agumurray/G8-TP1/firmware_v3/documentation/firmware/eclipse/Eclipse-Win14.png

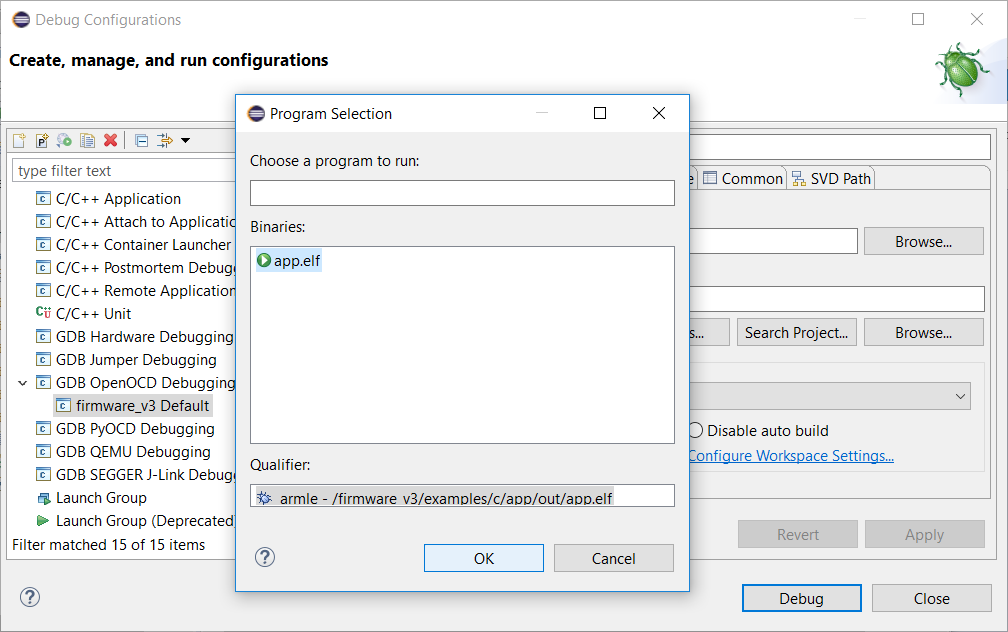
firmware_v3/documentation/firmware/eclipse/Eclipse-Win14.png
