agumurray/G8-TP1/firmware_v3/documentation/firmware/eclipse/targets-02.png

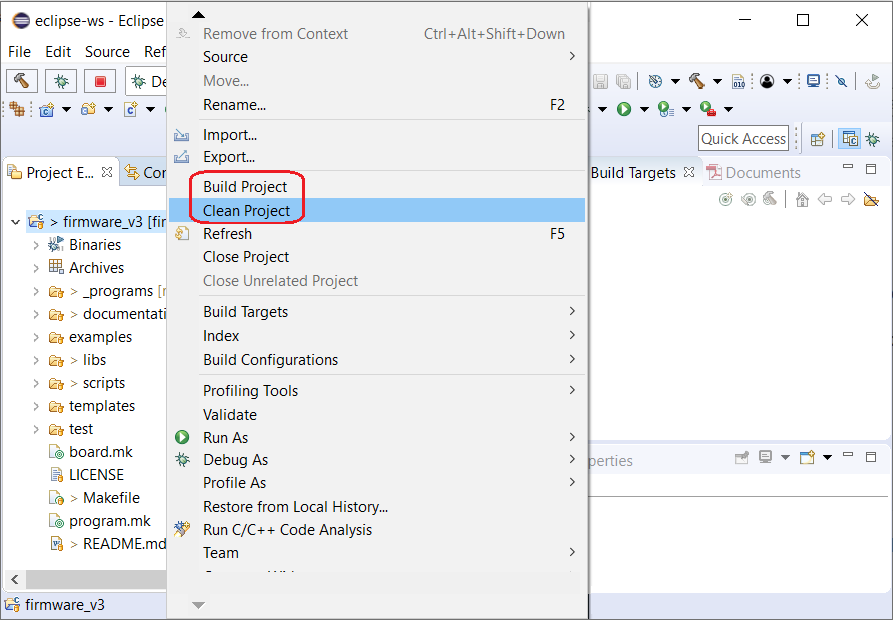
firmware_v3/documentation/firmware/eclipse/targets-02.png
