agumurray/G8-TP1/firmware_v3/documentation/firmware/embedded_ide/open02.png

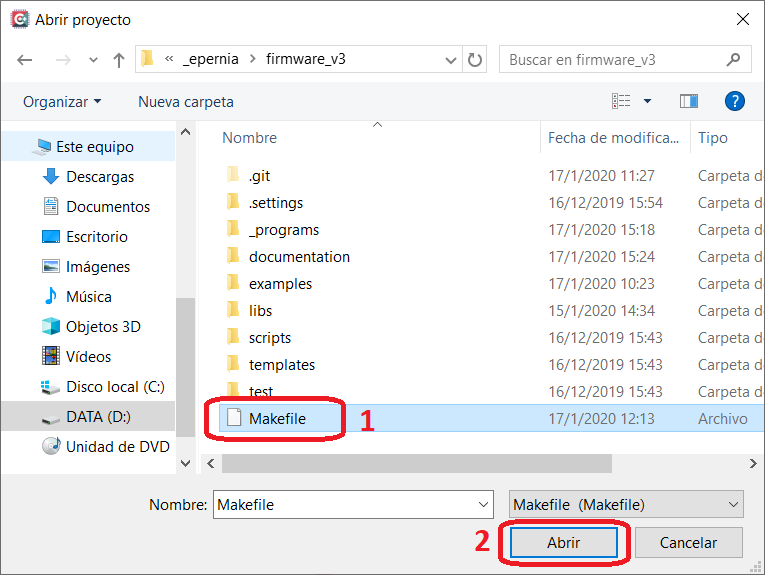
firmware_v3/documentation/firmware/embedded_ide/open02.png
