agumurray/G8-TP1/firmware_v3/test/test_hcsr04/sapi/adc_dac/adc_analog_stick_connection.png

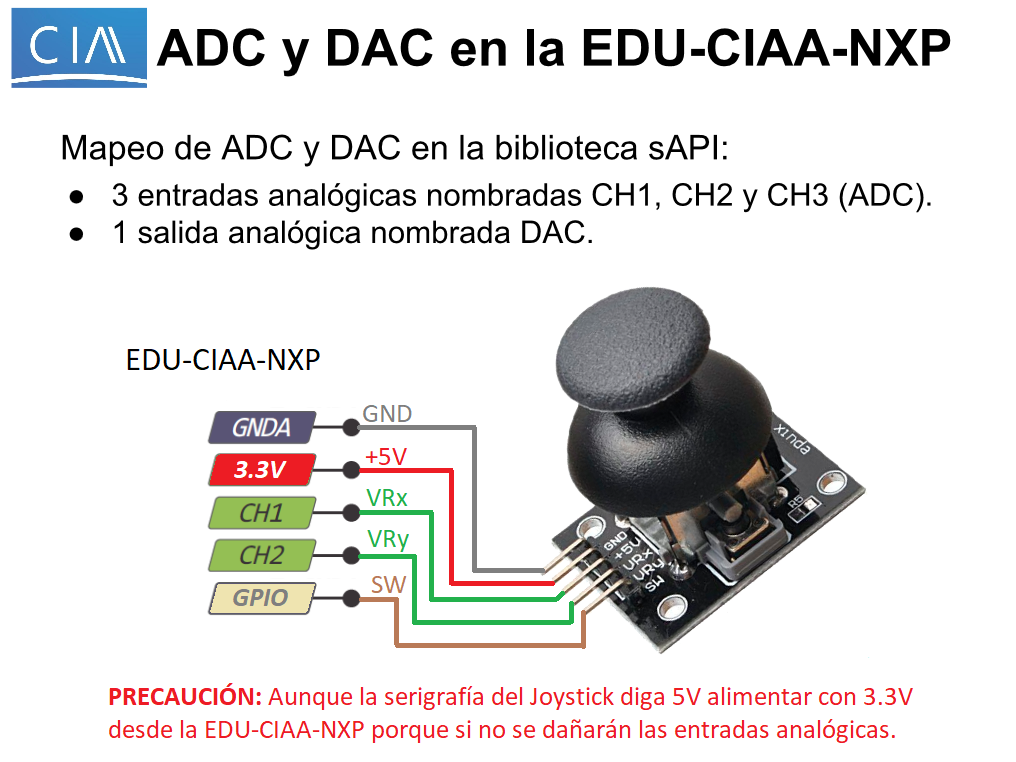
firmware_v3/test/test_hcsr04/sapi/adc_dac/adc_analog_stick_connection.png
