agumurray/G8-TP1/firmware_v3/test/test_hcsr04/sapi/bluetooth/hc05_uart_bridge/bluetooth_hc05_connection.png

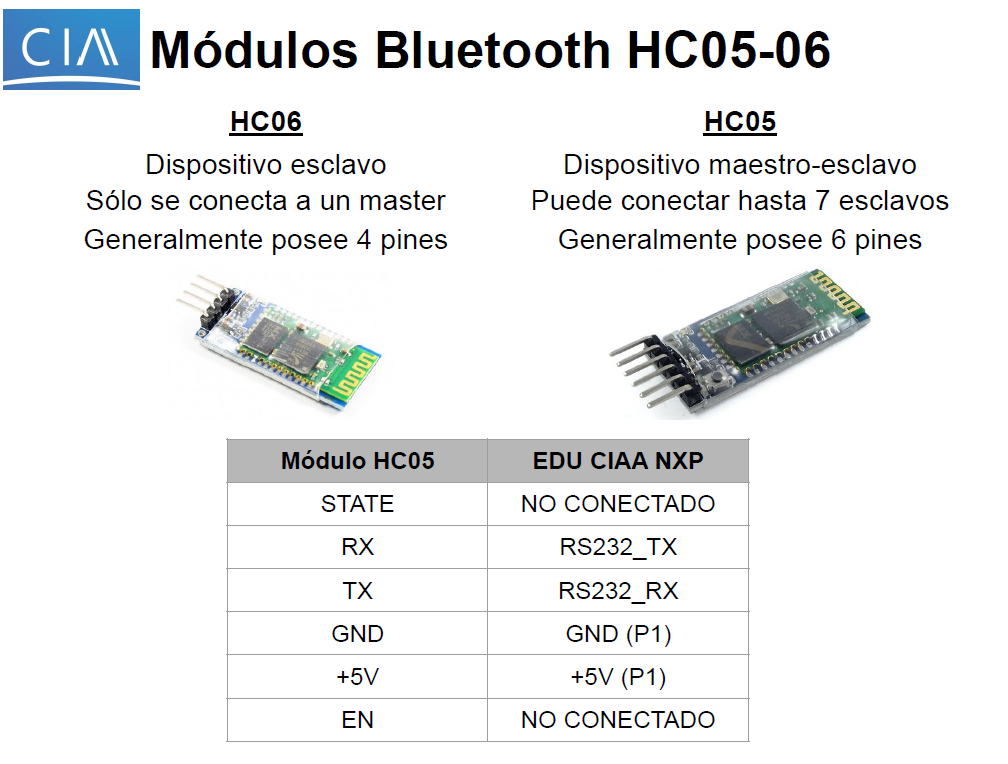
firmware_v3/test/test_hcsr04/sapi/bluetooth/hc05_uart_bridge/bluetooth_hc05_connection.png
