agumurray/G8-TP1/firmware_v3/test/test_hcsr04/sapi/bluetooth/hm10_uart_bridge/bluetooth_ble_hm10_connection.png

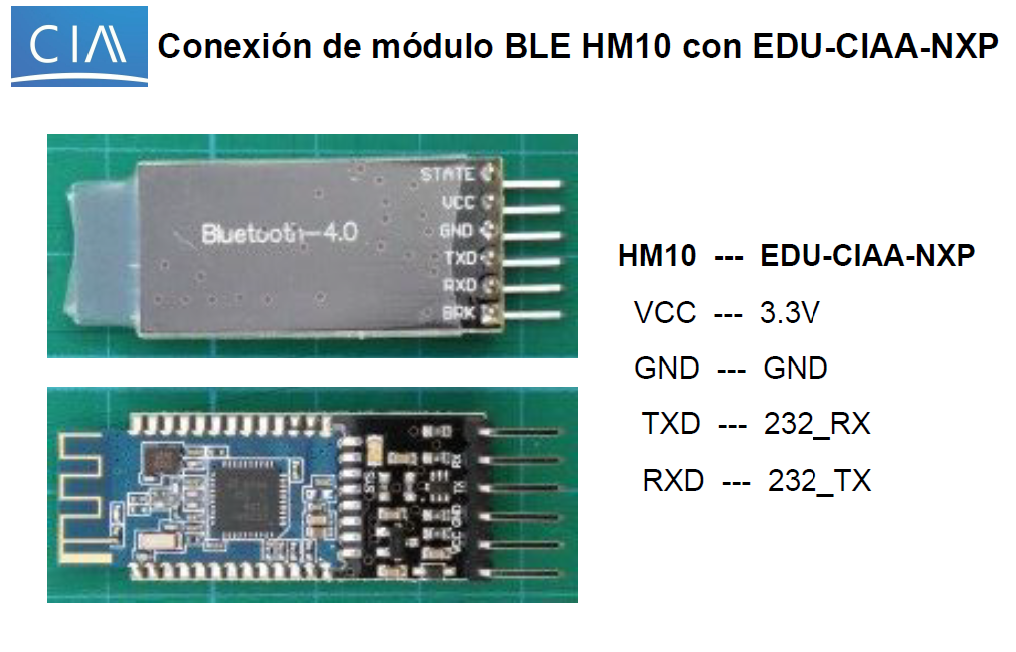
firmware_v3/test/test_hcsr04/sapi/bluetooth/hm10_uart_bridge/bluetooth_ble_hm10_connection.png
