agumurray/G8-TP1/firmware_v3/test/test_hcsr04/sapi/dht11_temp_humidity/DHT11 and EDU-CIAA-NXP.png

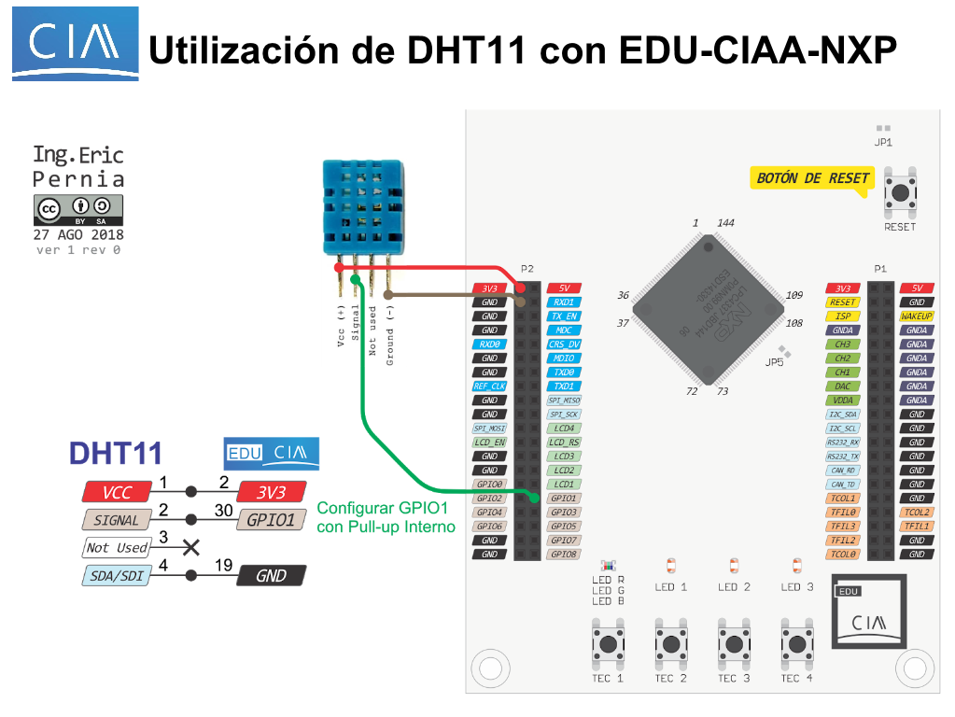
firmware_v3/test/test_hcsr04/sapi/dht11_temp_humidity/DHT11 and EDU-CIAA-NXP.png
