agumurray/G8-TP1/firmware_v3/test/test_hcsr04/sapi/fatfs_sdcard_usbmsd/SD SPI.png

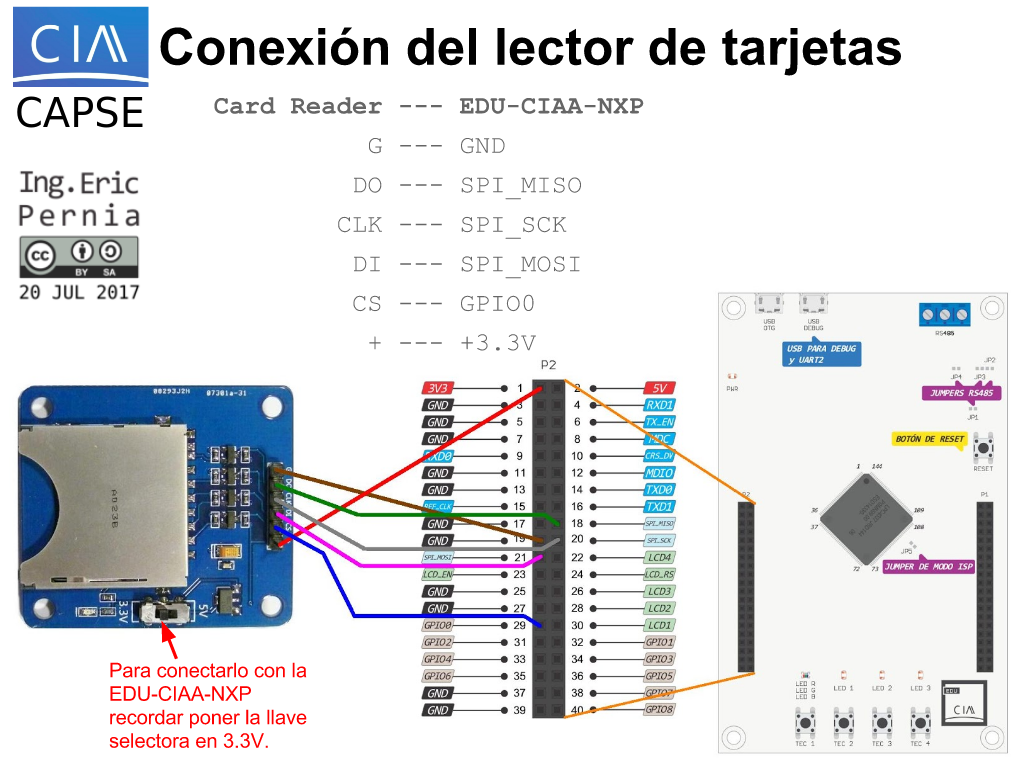
firmware_v3/test/test_hcsr04/sapi/fatfs_sdcard_usbmsd/SD SPI.png
