agumurray/G8-TP1/firmware_v3/test/test_hcsr04/sapi/gpio/axis_interface/AXI Stream.png

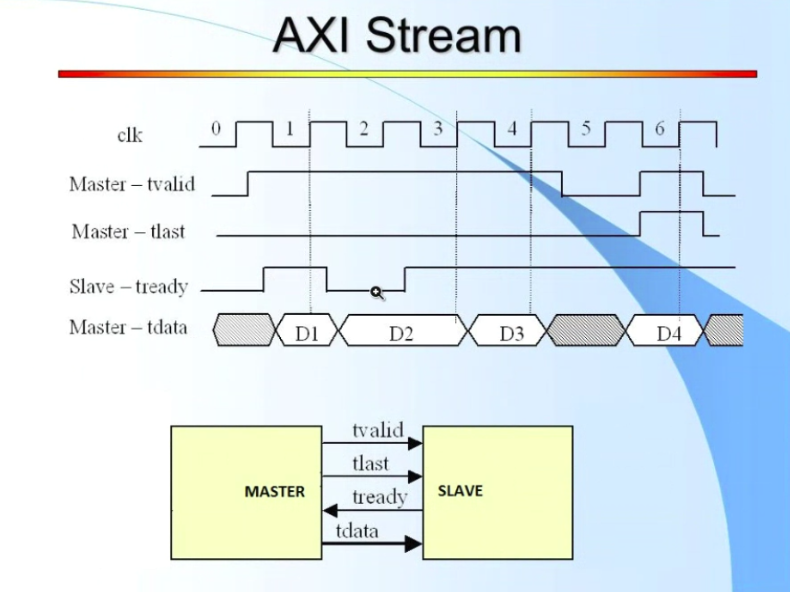
firmware_v3/test/test_hcsr04/sapi/gpio/axis_interface/AXI Stream.png
