agumurray/G8-TP1/firmware_v3/test/test_hcsr04/sapi/gpio/axis_interface/axis_pins_edu_ciaa.png

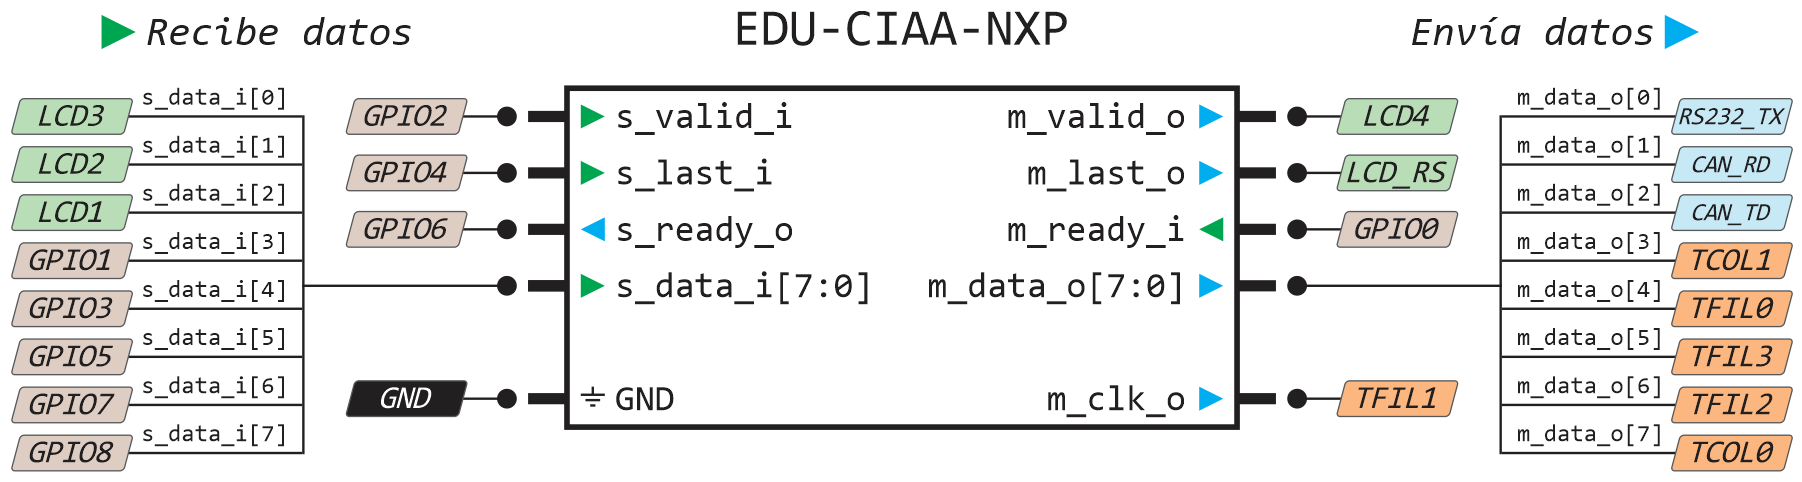
firmware_v3/test/test_hcsr04/sapi/gpio/axis_interface/axis_pins_edu_ciaa.png
