agumurray/G8-TP1/firmware_v3/test/test_hcsr04/sapi/hcsr04_ultrasonic_sensor/Conexión EDU-CIAA - HC-SR04.png

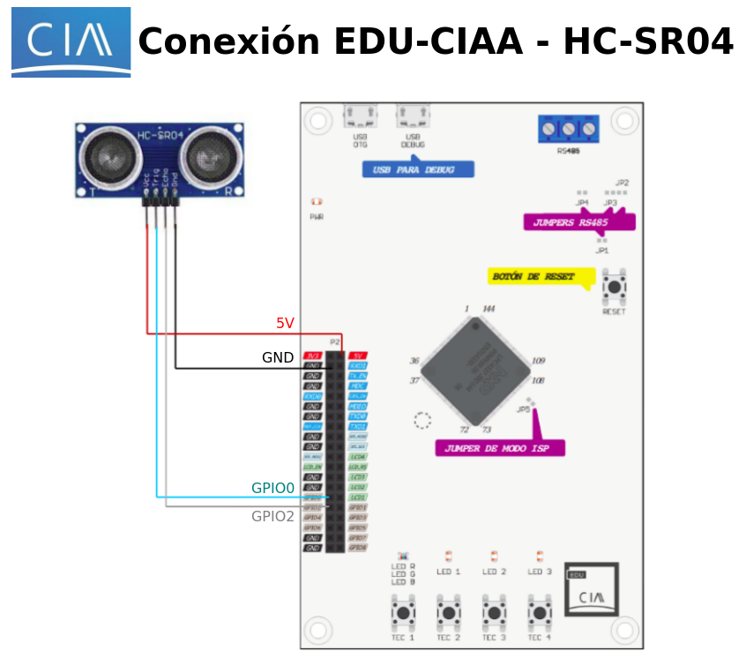
firmware_v3/test/test_hcsr04/sapi/hcsr04_ultrasonic_sensor/Conexión EDU-CIAA - HC-SR04.png
