agumurray/G8-TP1/firmware_v3/test/test_hcsr04/sapi/i2c/IMUs/mpu9250/MPU9250 and EDU-CIAA-NXP.png

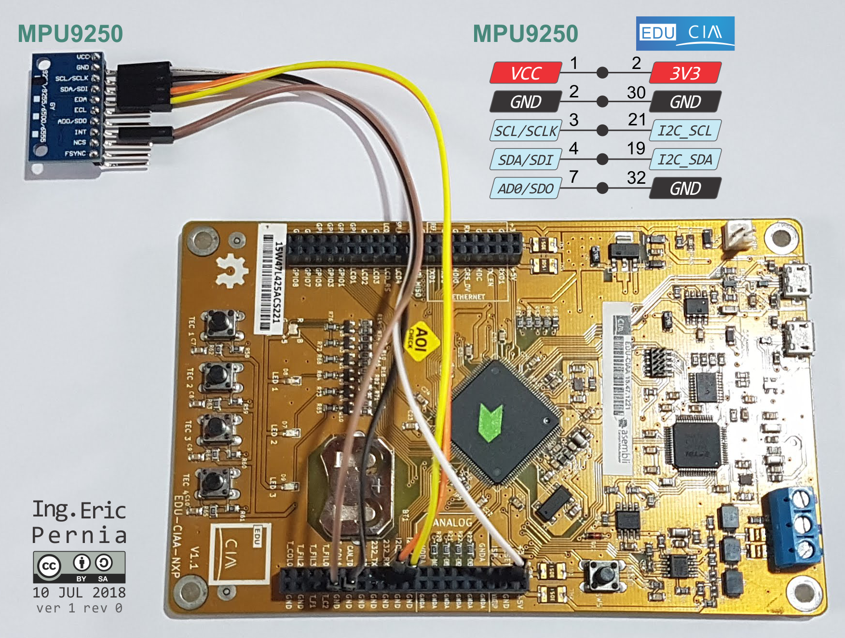
firmware_v3/test/test_hcsr04/sapi/i2c/IMUs/mpu9250/MPU9250 and EDU-CIAA-NXP.png
