agumurray/G8-TP1/firmware_v3/test/test_hcsr04/sapi/i2c/IMUs/mpu9250/Serial Terminal - MPU9250 working.PNG

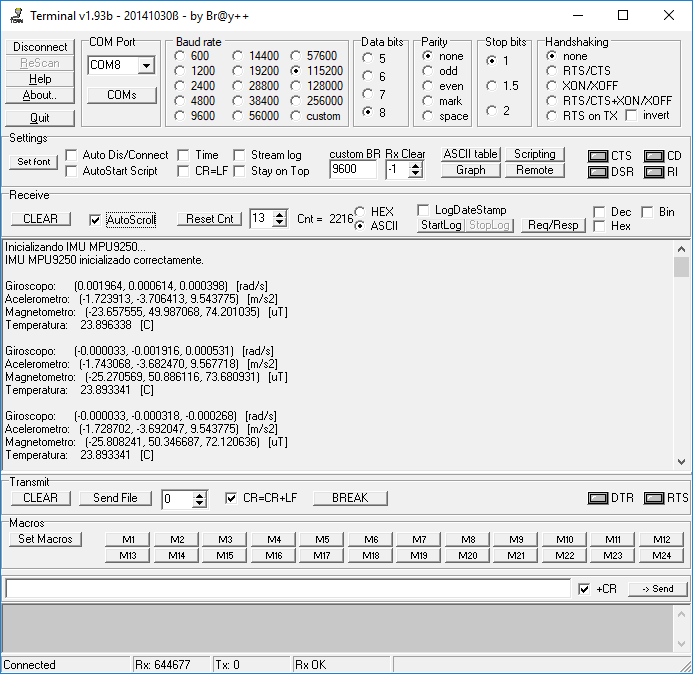
firmware_v3/test/test_hcsr04/sapi/i2c/IMUs/mpu9250/Serial Terminal - MPU9250 working.PNG
