agumurray/G8-TP1/firmware_v3/test/test_hcsr04/sapi/i2c/magnetometers/hmc5883l/HMC5883L_EDU-CIAA.png

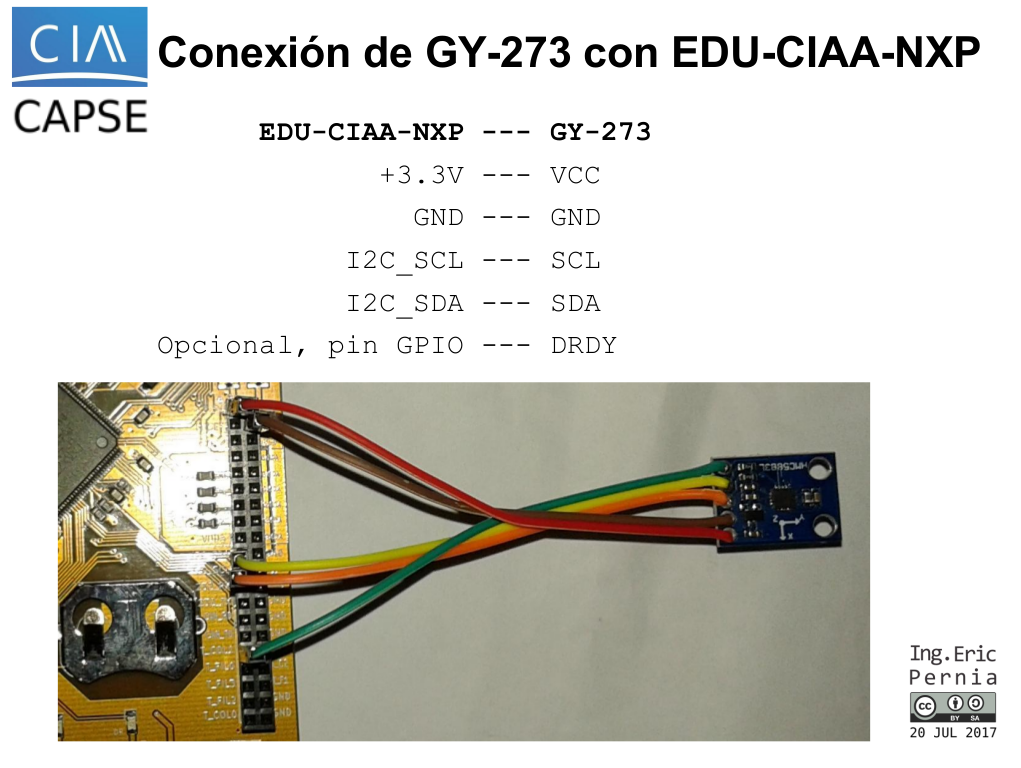
firmware_v3/test/test_hcsr04/sapi/i2c/magnetometers/hmc5883l/HMC5883L_EDU-CIAA.png
