agumurray/G8-TP1/firmware_v3/test/test_hcsr04/sapi/keypad_7segment/7 segment display - EDU-CIAA-NXP.png

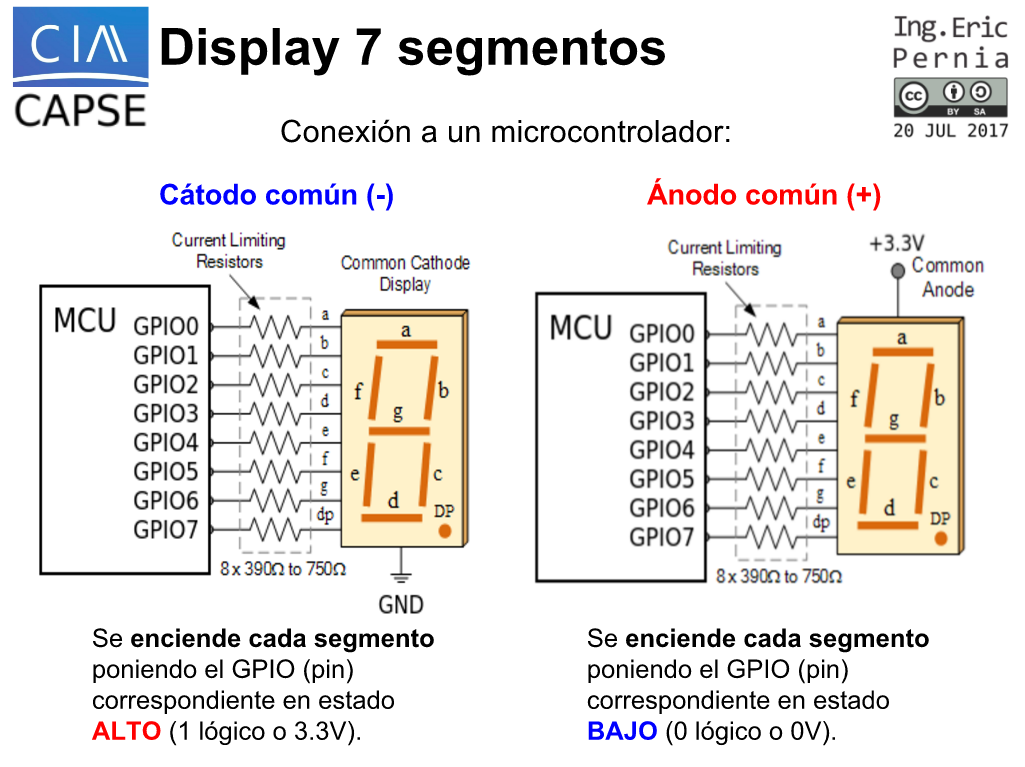
firmware_v3/test/test_hcsr04/sapi/keypad_7segment/7 segment display - EDU-CIAA-NXP.png
