agumurray/G8-TP1/firmware_v3/test/test_hcsr04/sapi/lcd/lcd info/LCD HD44780 connection.png

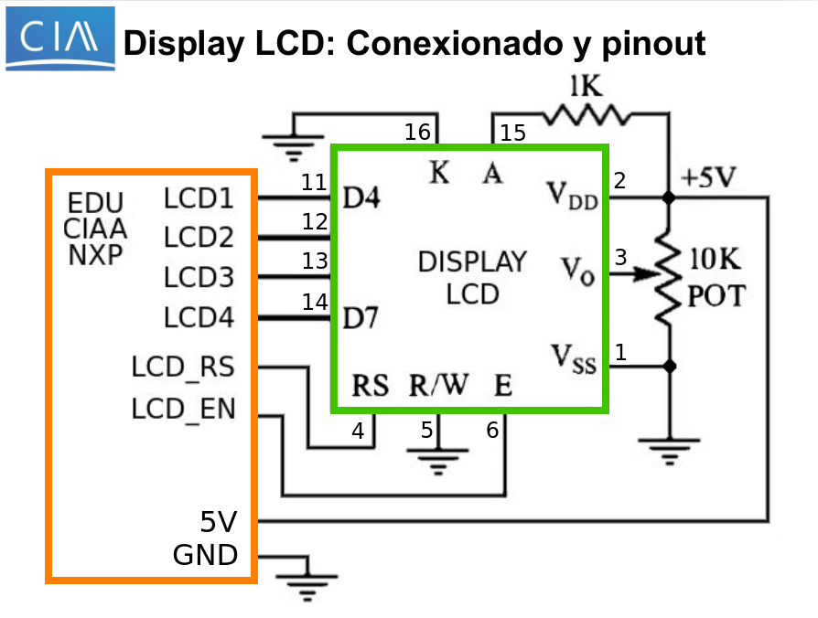
firmware_v3/test/test_hcsr04/sapi/lcd/lcd info/LCD HD44780 connection.png
