agumurray/G8-TP1/firmware_v3/test/test_hcsr04/sapi/lcd/lcd_i2c/I2C expander PCF8574/Encapsulado en placa.png

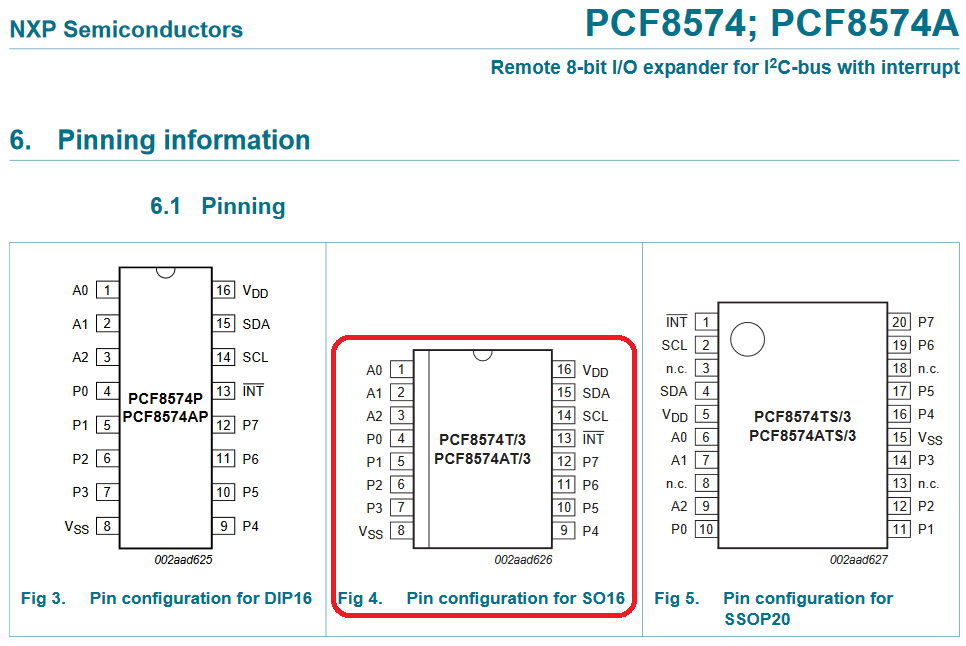
firmware_v3/test/test_hcsr04/sapi/lcd/lcd_i2c/I2C expander PCF8574/Encapsulado en placa.png
