agumurray/G8-TP1/firmware_v3/test/test_hcsr04/sapi/servo/servo_connection.png

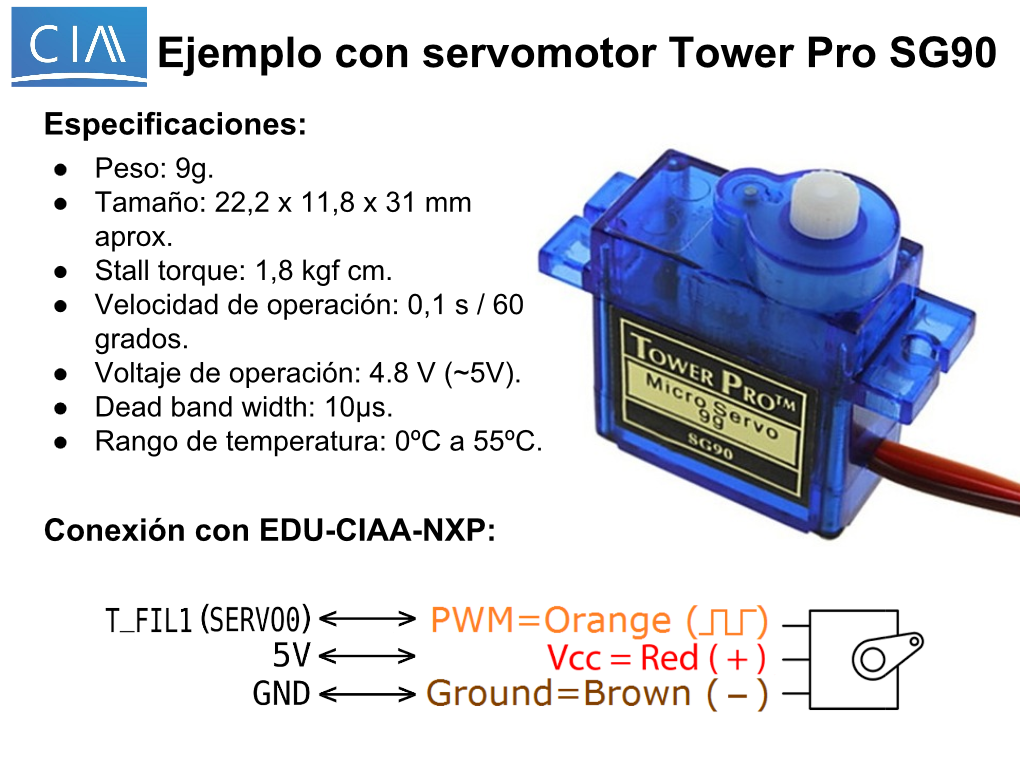
firmware_v3/test/test_hcsr04/sapi/servo/servo_connection.png
