agumurray/G8-TP1/firmware_v3/test/test_hcsr04/sapi/servo/servo_pins.png

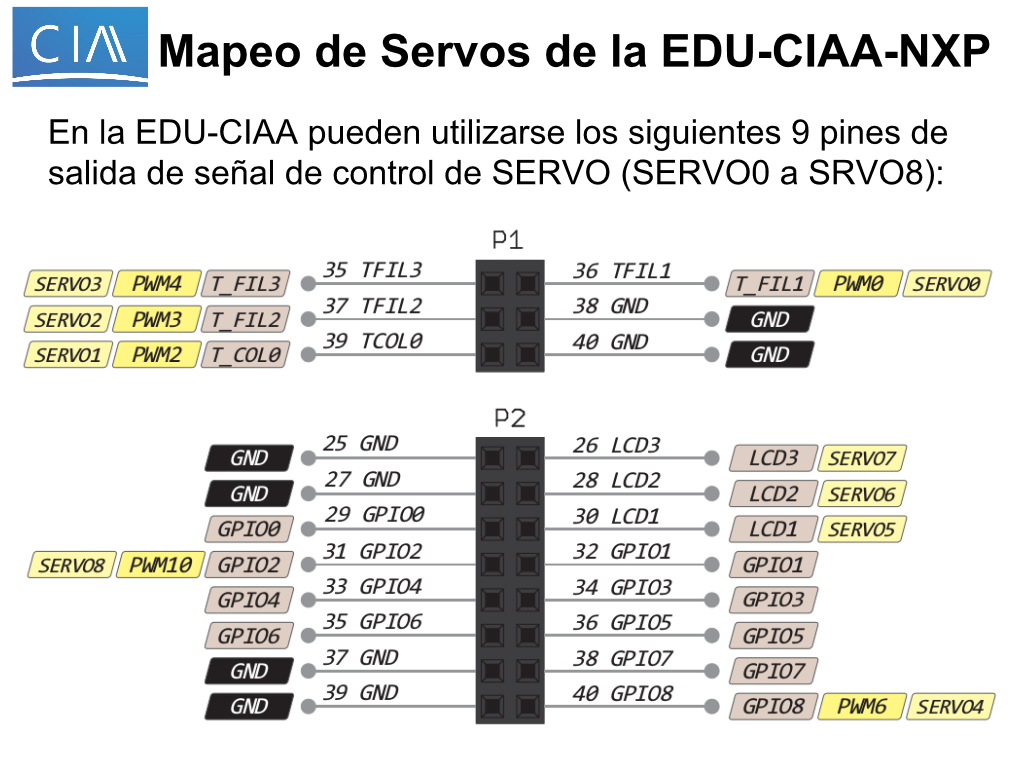
firmware_v3/test/test_hcsr04/sapi/servo/servo_pins.png
