agumurray/G8-TP1/firmware_v3/test/test_hcsr04/sapi/wifi/esp8266/Conexion ESP8266 y EDU-CIAA.png

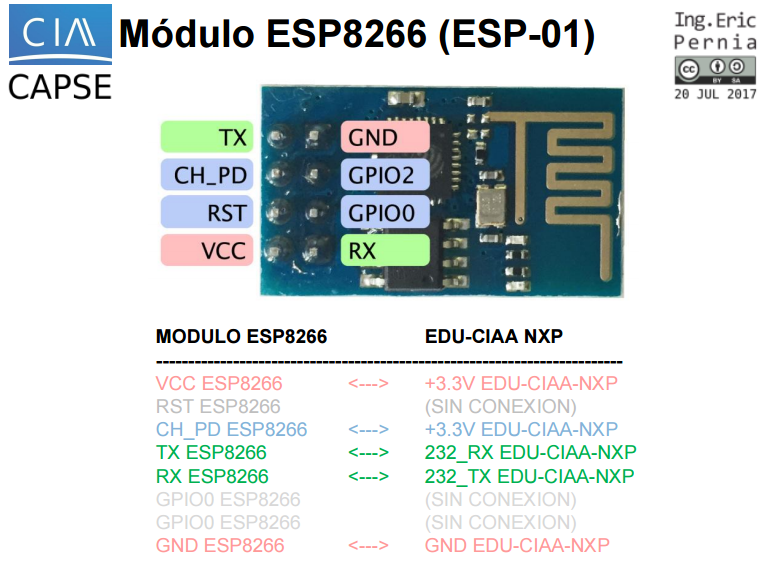
firmware_v3/test/test_hcsr04/sapi/wifi/esp8266/Conexion ESP8266 y EDU-CIAA.png
