agumurray/G8-TP1/firmware_v3/test/test_hcsr04/sapi/wifi/esp8266/iot_thingspeak/Datos en Thingspeak.png

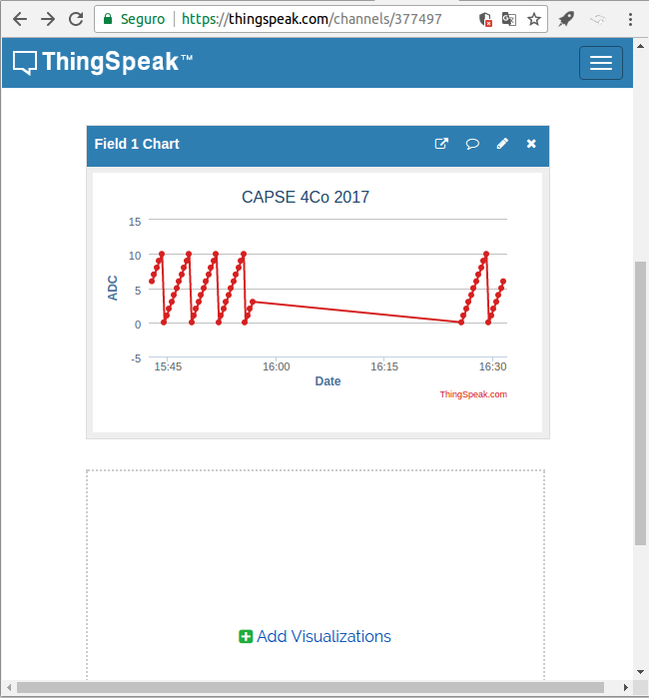
firmware_v3/test/test_hcsr04/sapi/wifi/esp8266/iot_thingspeak/Datos en Thingspeak.png
