agumurray/G8-TP1/firmware_v3/test/test_hcsr04/sapi/adc_dac/EDU-CIAA-NXP Tiras de pines y Potenciómetro.pdf

## EDU-CIAA-NXP Preparación de placa con Tiras de pines hembra y Potenciómetro

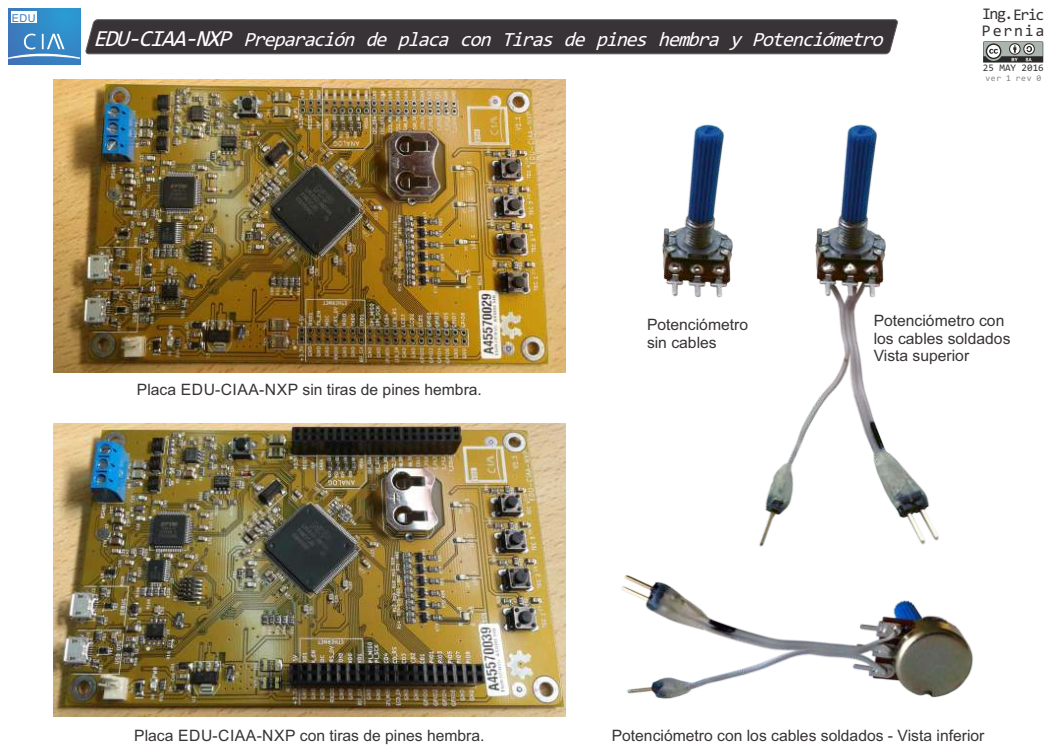
[picture p180: page 1]
EDU; Potenciómetro sin cables; 25 MAY 2016 ver 1 rev 0; Pernia; Ing.Eric

Potenciómetro con
los cables soldados
Vista superior

Placa EDU-CIAA-NXP sin tiras de pines hembra.

Placa EDU-CIAA-NXP con tiras de pines hembra.

Potenciómetro con los cables soldados - Vista inferior

## EDU-CIAA-NXP Conexión de potenciómetro

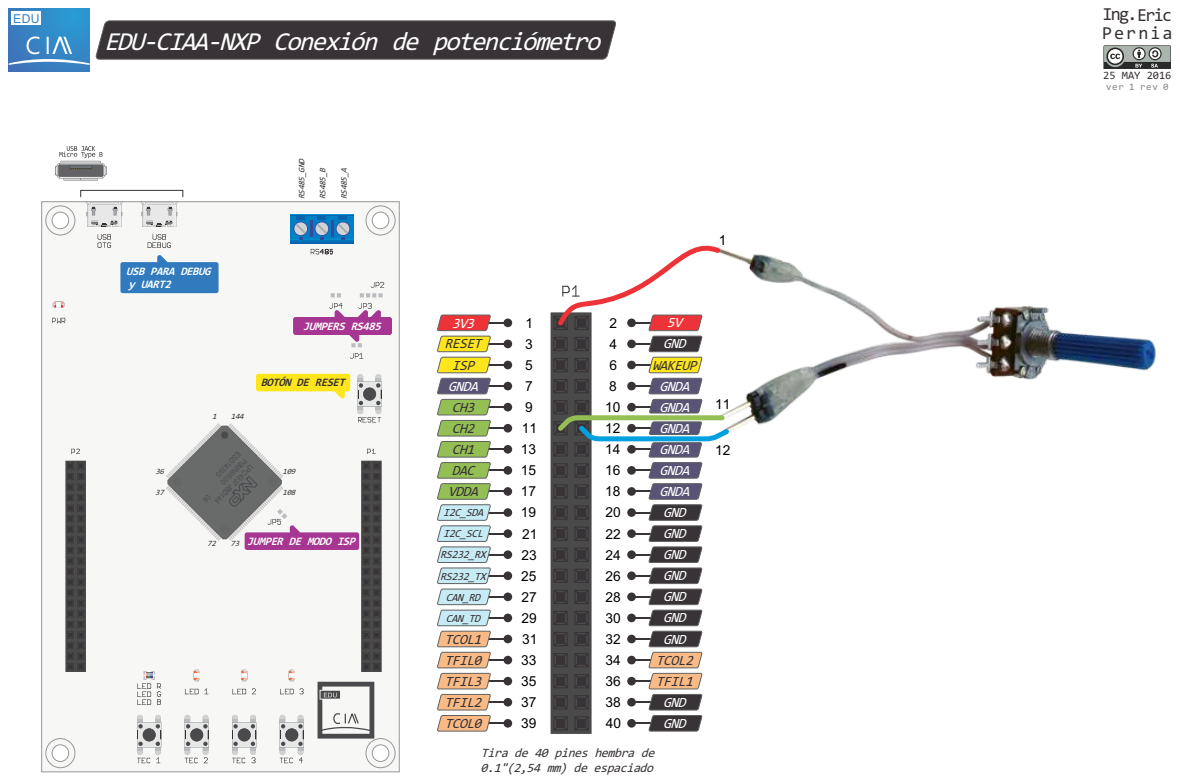
[picture p181: page 2]
EDU; 25 MAY 2016 ver 1 rev 0; Pernia; Ing.Eric; LPC4337 JBD144; ESD14330-; JUMPER DE MODO ISP; JUMPERS RS485; RS485_GND; GND; GNDA; WAKEUP; TCOL2; TFIL1; TCOL1; TFIL0; TFIL3; TFIL2; TCOL0; ISP; RESET; DAC; VDDA; I2C_SDA; I2C_SCL; CAN_RD; CAN_TD

USB PARA DEBUG
y UART2

BOTÓN DE RESET

Tira de 40 pines hembra de
0.1"(2,54 mm) de espaciado
