agumurray/G8-TP1/firmware_v3/documentation/CIAA_Boards/NXP_LPC4337/CIAA-NXP/CIAA-NXP Esquematico.pdf

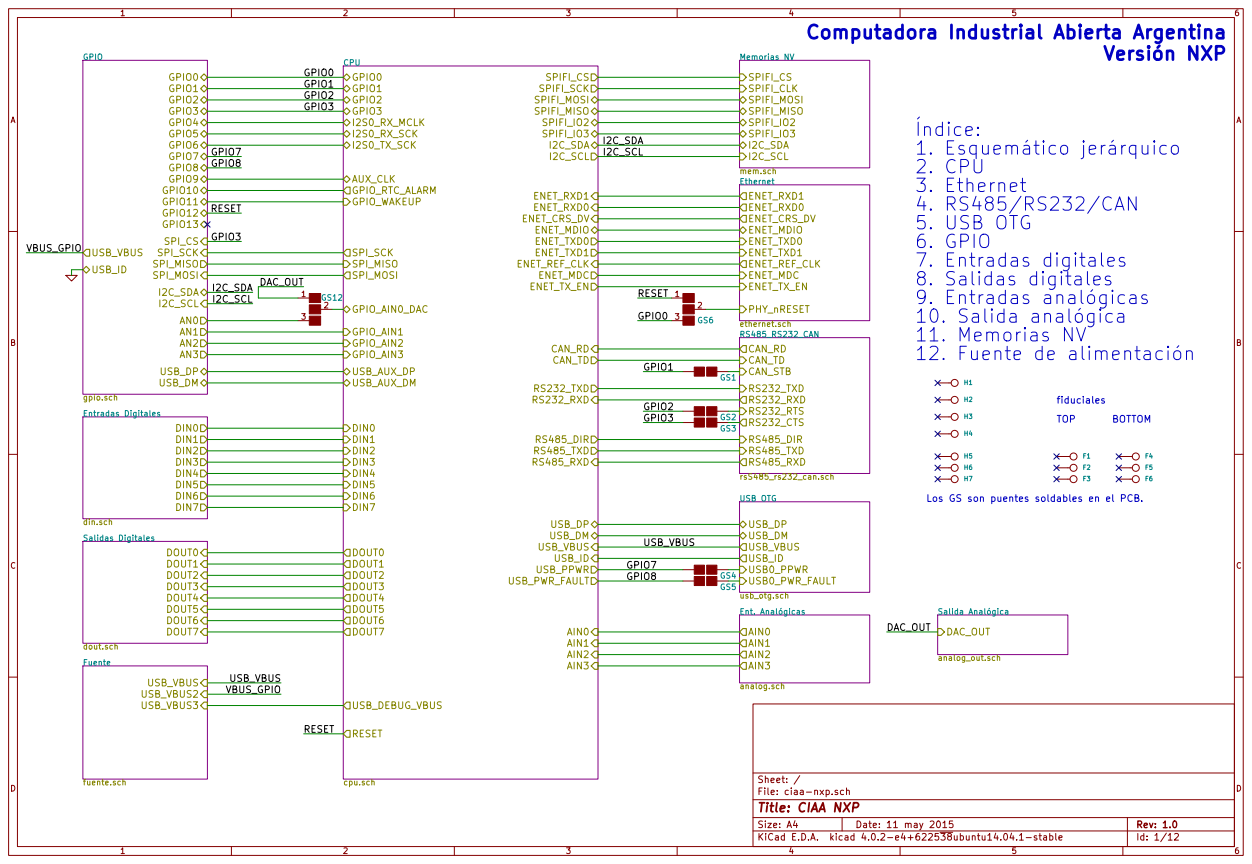
[picture p182: page 1]

Computadora Industrial Abierta Argentina

GPIO1
GPIO2
GPIO3

File: ciaa-nxp.sch Sheet: /
Id: 1/12 Title: CIAA NXP

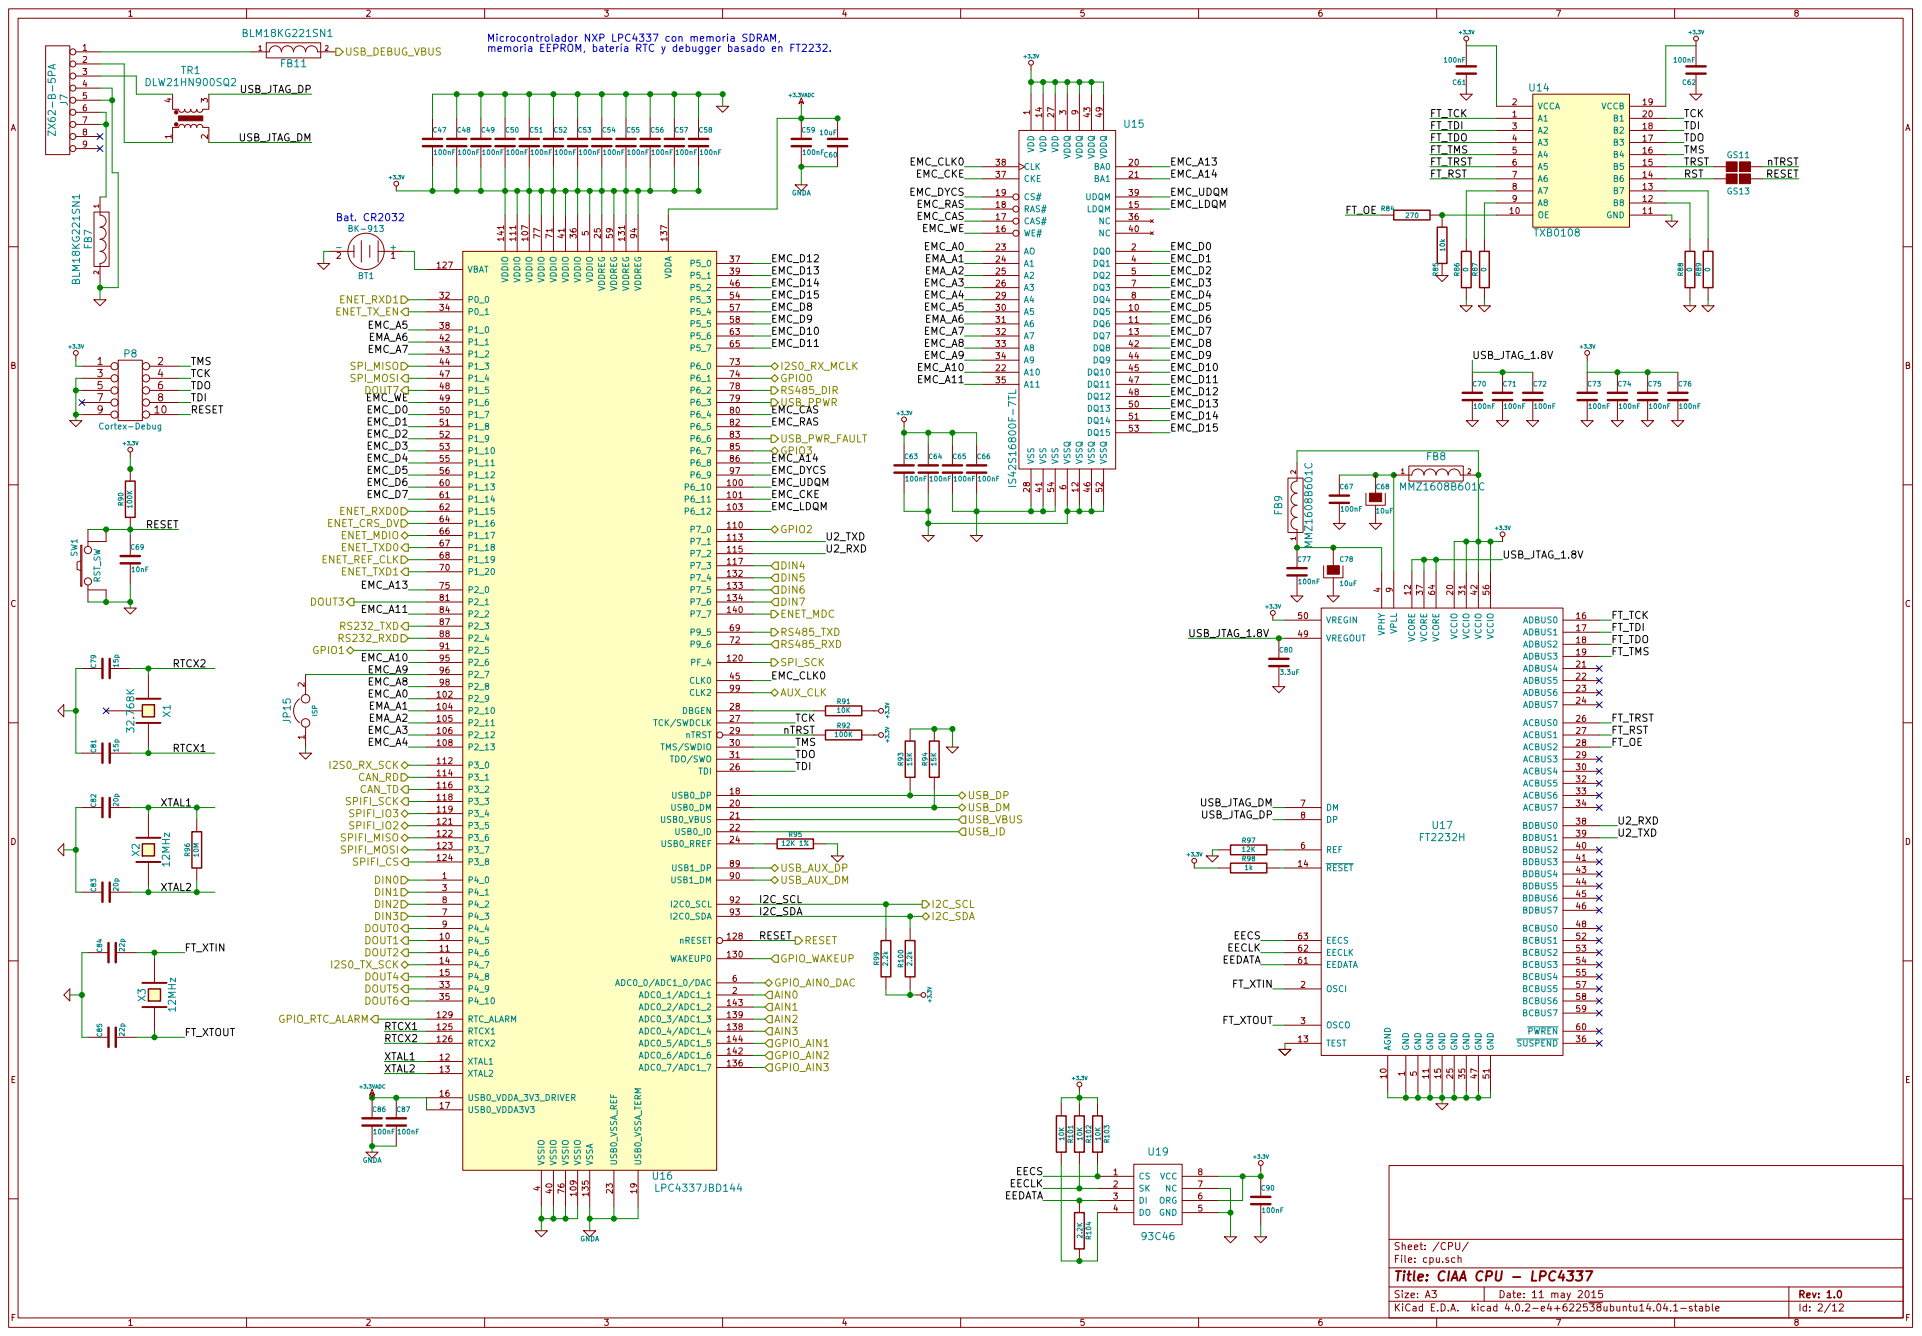
[picture p183: page 2]

memoria EEPROM, batería RTC y debugger basado en FT2232.

9 DQ5 10 BA0 20 A5 30 NC 40 DQ13 50 DQ6 11 BA1 21 A6 31 VSS 41 DQ14 51 VSSQ 12 A10 22 A7 32 DQ8 42 VSSQ 52 DQ7 13 AO 23 A8 33 VDDQ 43 DQ15 53 VDD 14 A1 24 A9 34 DQ9 44 VSS 54

FT_TMS | 20 GND 16 B3
FT_TDO | 17 B2

FT_TRST | | 15 B4
FT_RST | 14 B5

5 ADC0_0/ADC1_0/DAC 6 P4_3 7 P4_2 8 P4_4 9 P4_5 10 USB0_DM 20 TMS/SWDIO 30 VSSIO 40 P1_7 50 P1_13 60 P1_20 70 P6_4 80 USB1_DM 90 P4_6 11 USB0_VBUS 21 TDO/SWO 31 VDDIO 41 P1_8 51 P1_14 61 VDDIO 71 P2_1 81 P2_5 91 XTAL1 12 USB0_ID 22

9 AGND 10 VCCIO 20 ACBUS4 30 BDBUS2 40 VREGIN 50 PWREN 60 GND 11 ADBUS4 21 VCCIO 31 BDBUS3 41 GND 51 EEDATA 61 VCORE 12 ADBUS5 22 ACBUS5 32 VCCIO 42 BCBUS1 52 EECLK 62 TEST 13 ADBUS6 23 ACBUS6 33 BDBUS4 43 BCBUS2 53 EECS 63 RESET 14 ADBUS7 24 ACBUS7 34 BDBUS5 44 BCBUS3 54 VCORE 64 GND 15 GND 25 GND 35 BDBUS6 45 BCBUS4 55 ADBUS0 16 ACBUS0 26 SUSPEND 36 BDBUS7 46 VCCIO 56 ADBUS1 17 ACBUS1 27 VCORE 37 GND 47 BCBUS5 57 ADBUS2 18 ACBUS2 28 BDBUS0 38 BCBUS0 48 BCBUS6 58 ADBUS3 19 ACBUS3 29 BDBUS1 39 VREGOUT 49 BCBUS7 59 U17 FT2232H

5 REF 6 DM 7 DP 8 VPLL

File: cpu.sch Sheet: /CPU/
Id: 2/12 Title: CIAA CPU - LPC4337

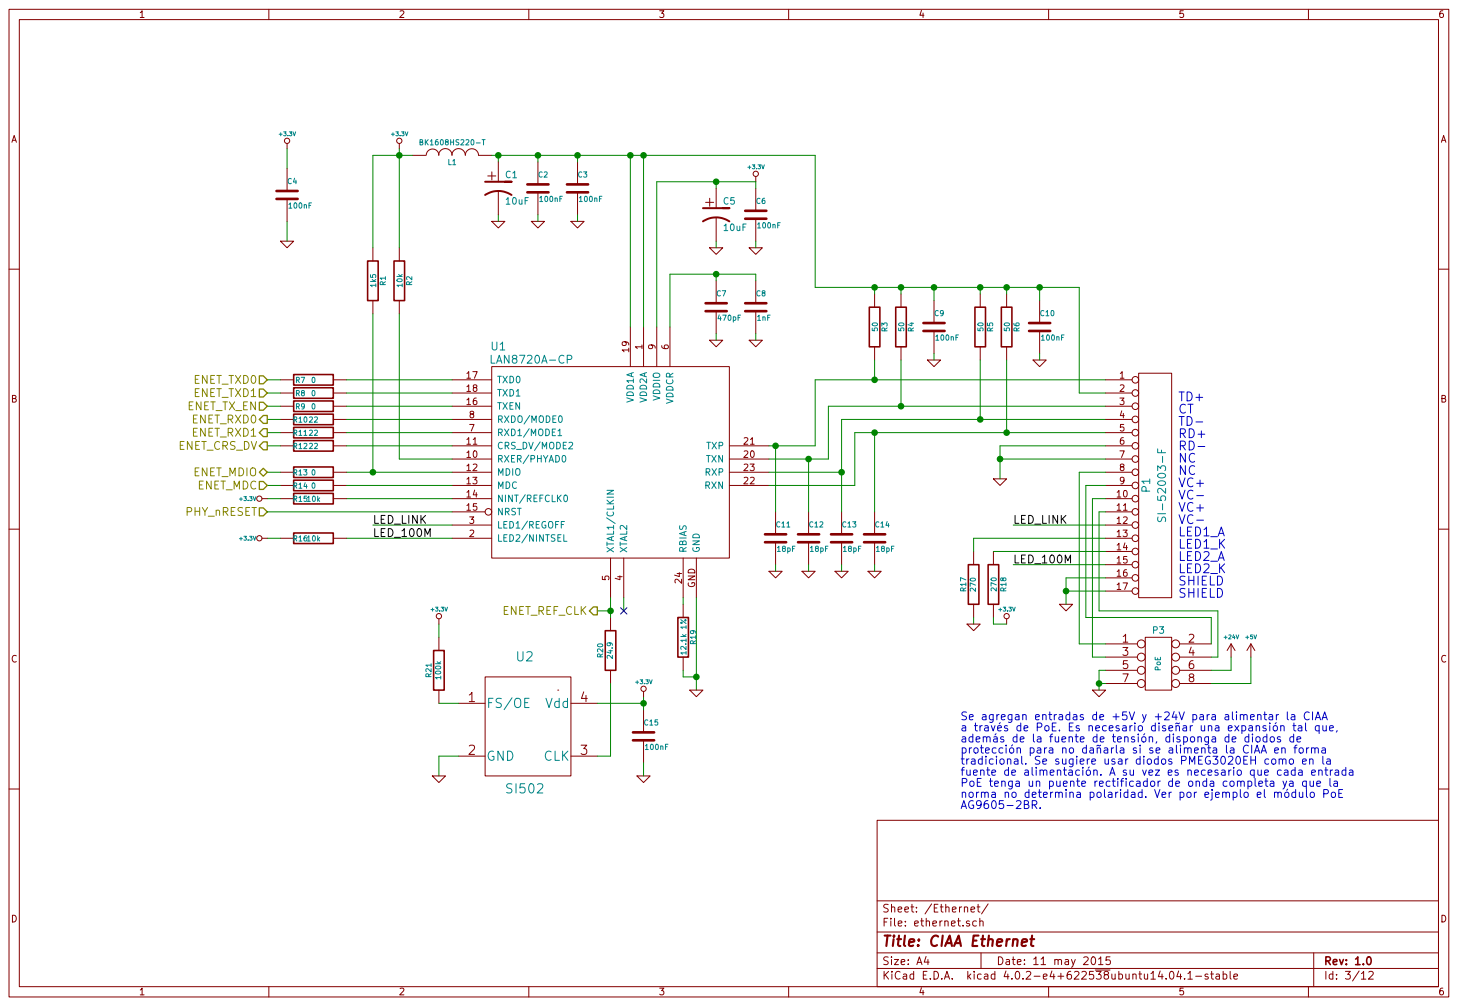
[picture p184: page 3]

9 RXER/PHYAD0 10 TXN 20 CRS_DV/MODE2 11 TXP 21 MDIO 12 RXN 22 MDC 13 RXP 23 NINT/REFCLK0 14 RBIAS 24 NRST 15 TXEN 16 TXD0 17 TXD1 18 VDD1A 19 GND GND U1
LAN8720A-CP

5 VDDCR
Id: 3/12 Title: CIAA Ethernet File: ethernet.sch Sheet: /Ethernet/ VDD2A

a través de PoE. Es necesario diseñar una expansión tal que,
además de la fuente de tensión, disponga de diodos de
protección para no dañarla si se alimenta la CIAA en forma
tradicional. Se sugiere usar diodos PMEG3020EH como en la
fuente de alimentación. A su vez es necesario que cada entrada
PoE tenga un puente rectificador de onda completa ya que la
norma no determina polaridad. Ver por ejemplo el módulo PoE

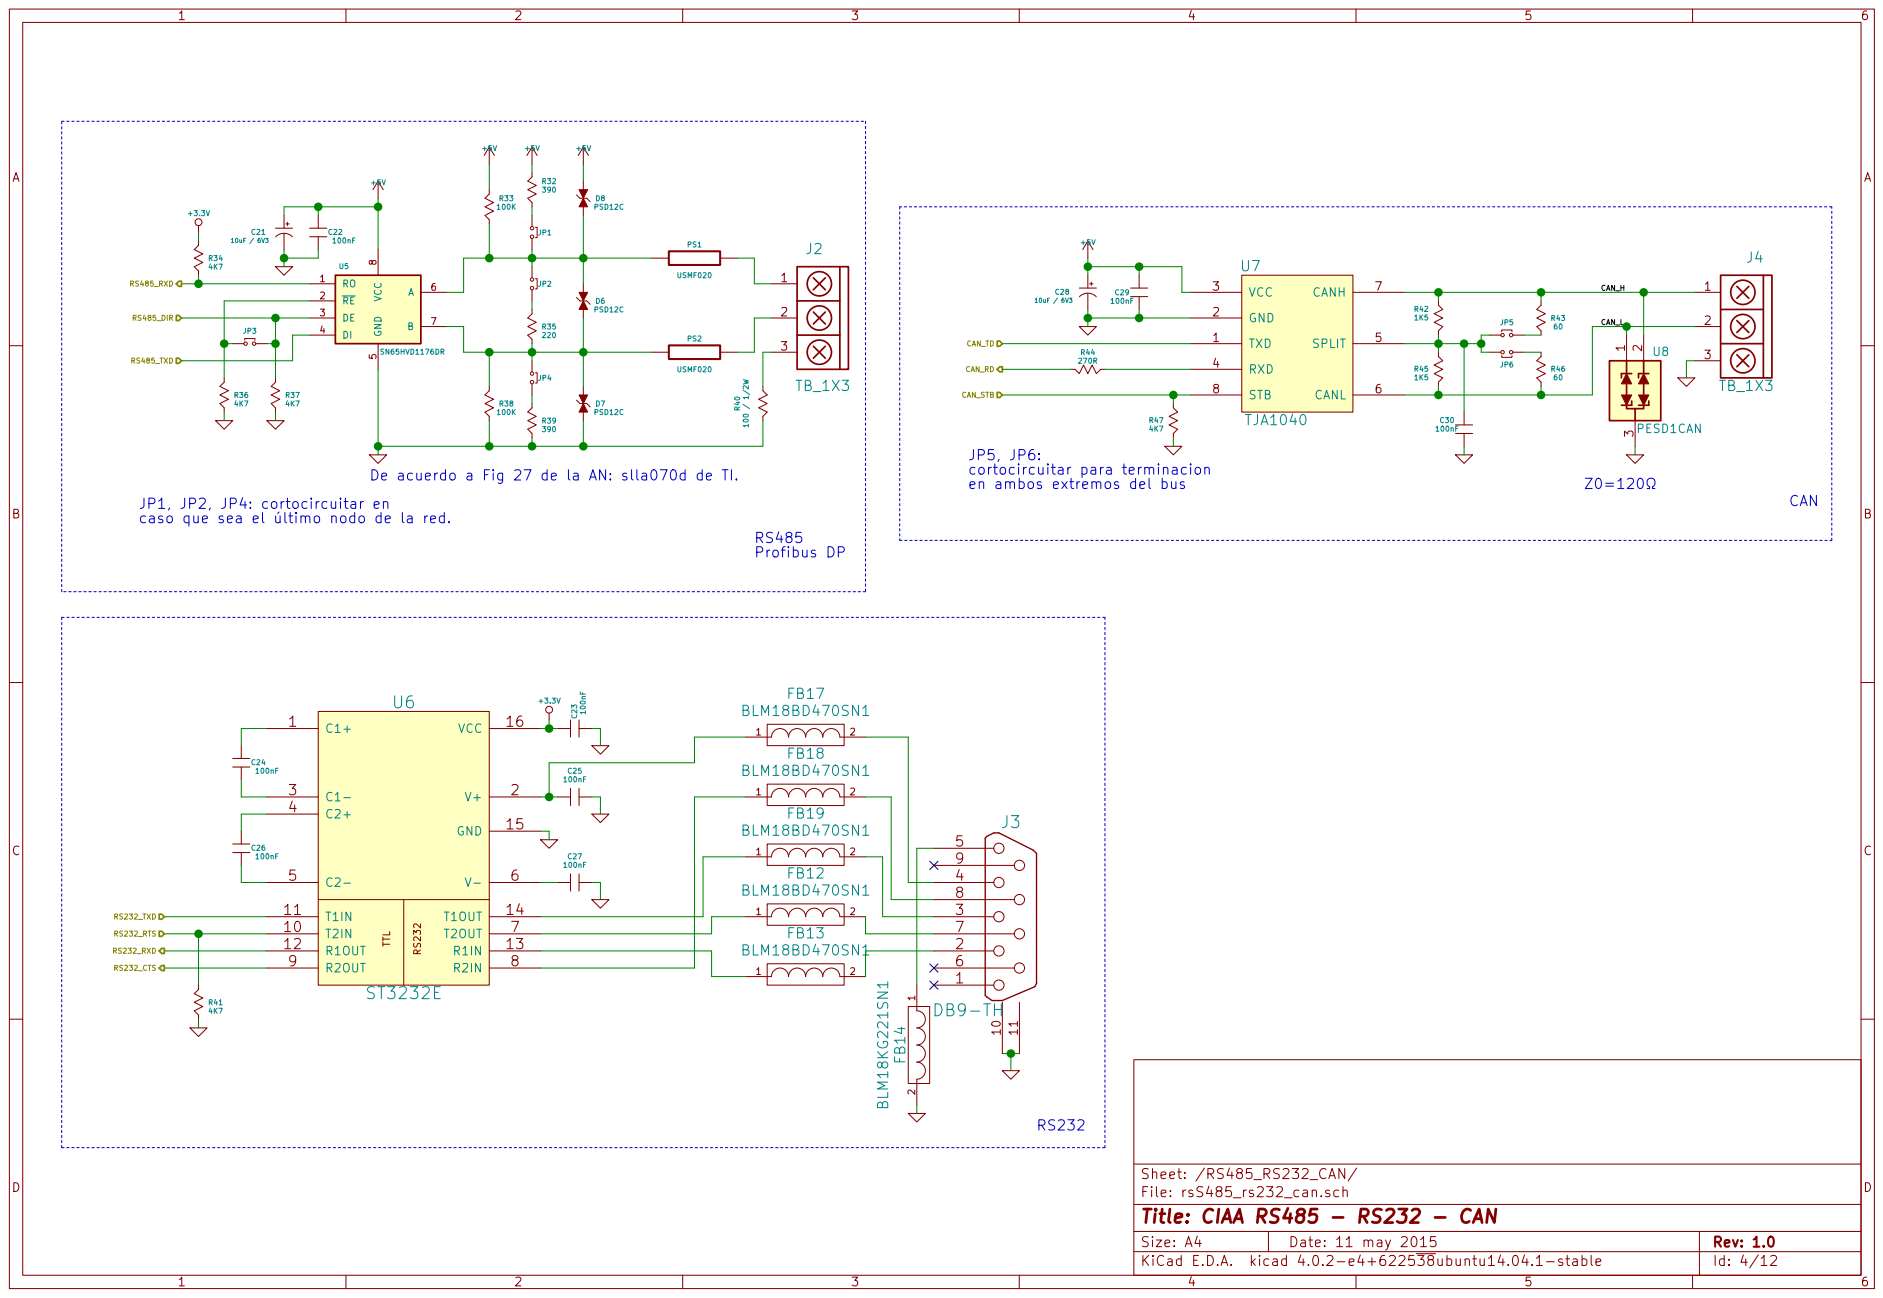
[picture p185: page 4]

caso que sea el último nodo de la red. R37

cortocircuitar para terminacion en ambos extremos del bus

De acuerdo a Fig 27 de la AN: slla070d de TI. R41

Sheet: /RS485_RS232_CAN/
File: rsS485_rs232_can.sch
Id: 4/12 Title: CIAA RS485 - RS232 - CAN

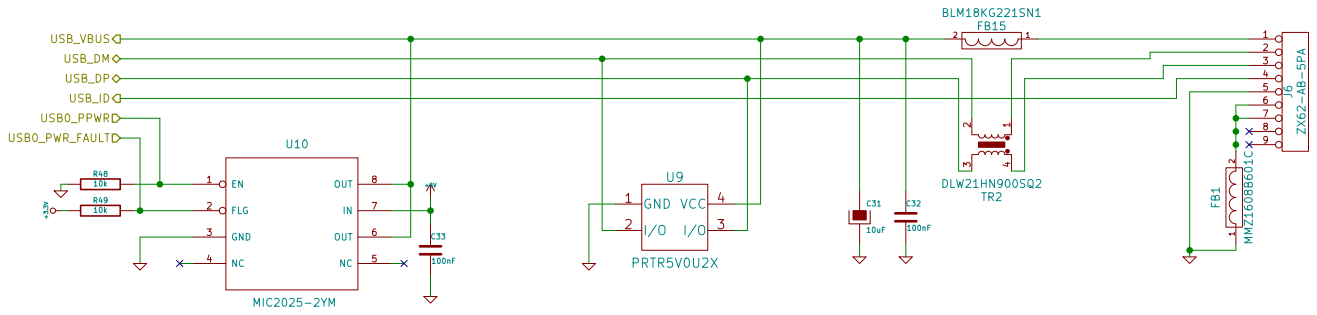
[picture p186: page 5]

Id: 5/12 Title: USB OTG CIAA

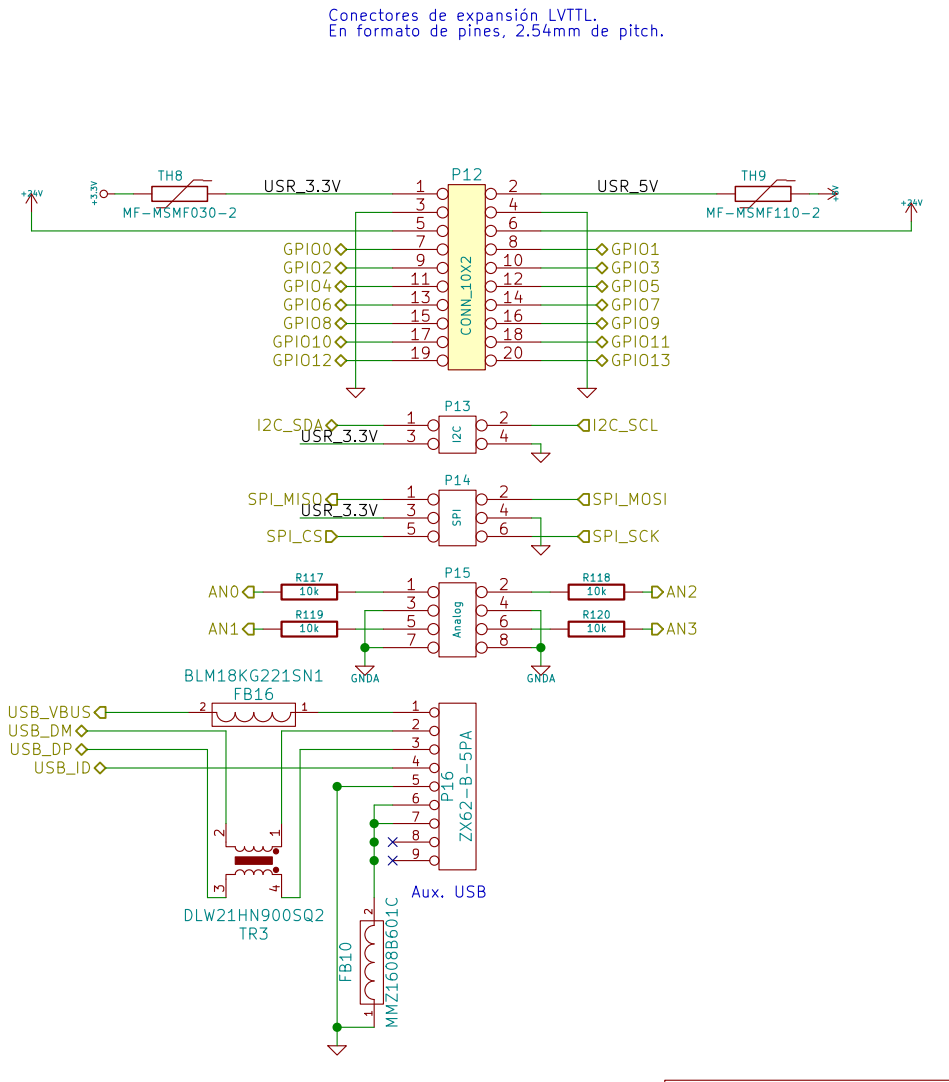
[picture p187: page 6]

Conectores de expansión LVTTL.

File: gpio.sch Sheet: /GPIO/
Id: 6/12 Title: CIAA GPIO/SPI/I2C/USB/ANALOG

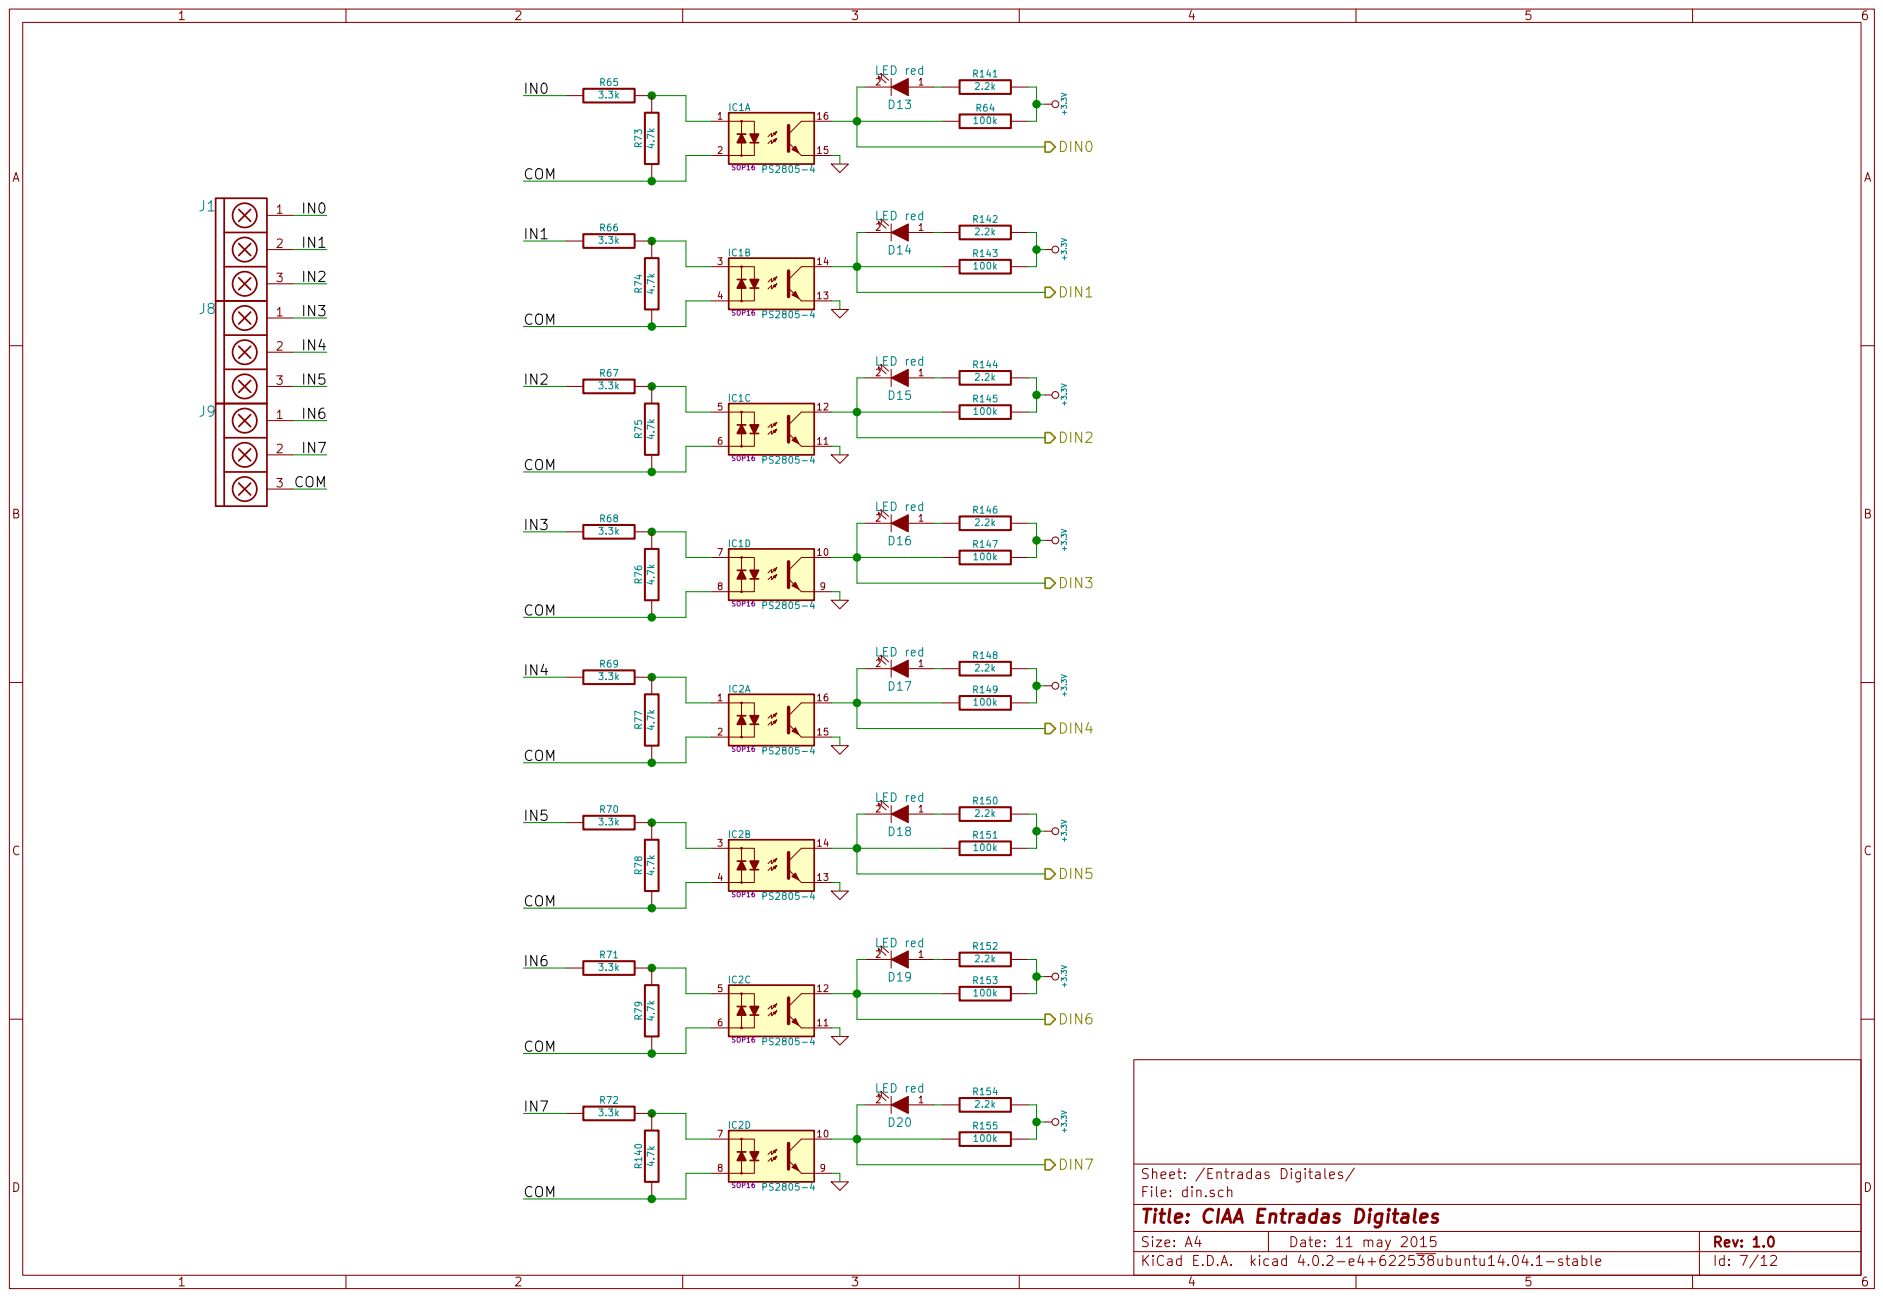
[picture p188: page 7]

File: din.sch Sheet: /Entradas Digitales/
Id: 7/12 Title: CIAA Entradas Digitales

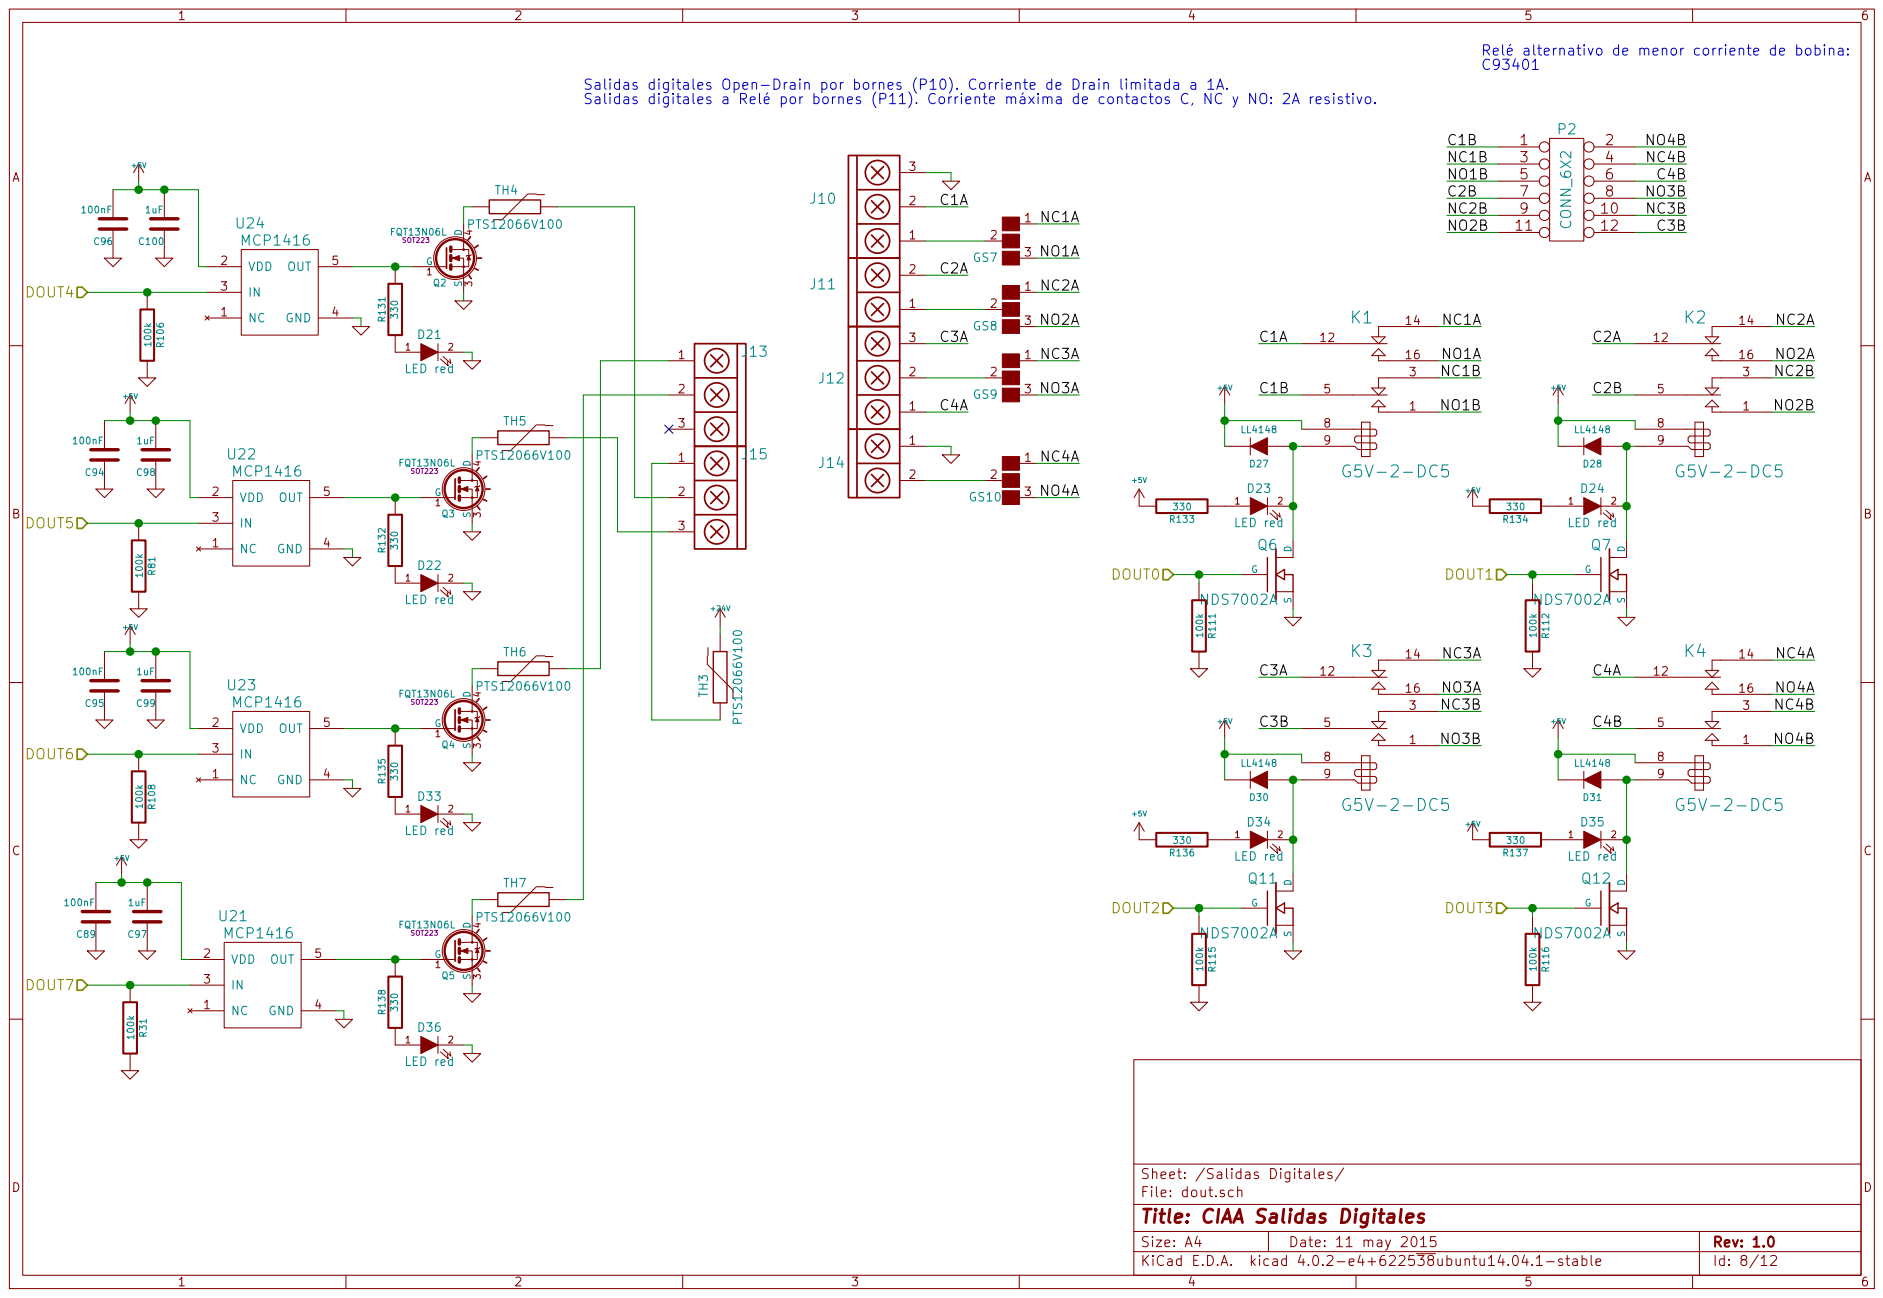
[picture p189: page 8]

Relé alternativo de menor corriente de bobina:

Salidas digitales Open-Drain por bornes (P10). Corriente de Drain limitada a 1A.
Salidas digitales a Relé por bornes (P11). Corriente máxima de contactos C, NC y NO: 2A resistivo.

File: dout.sch Sheet: /Salidas Digitales/
Id: 8/12 Title: CIAA Salidas Digitales

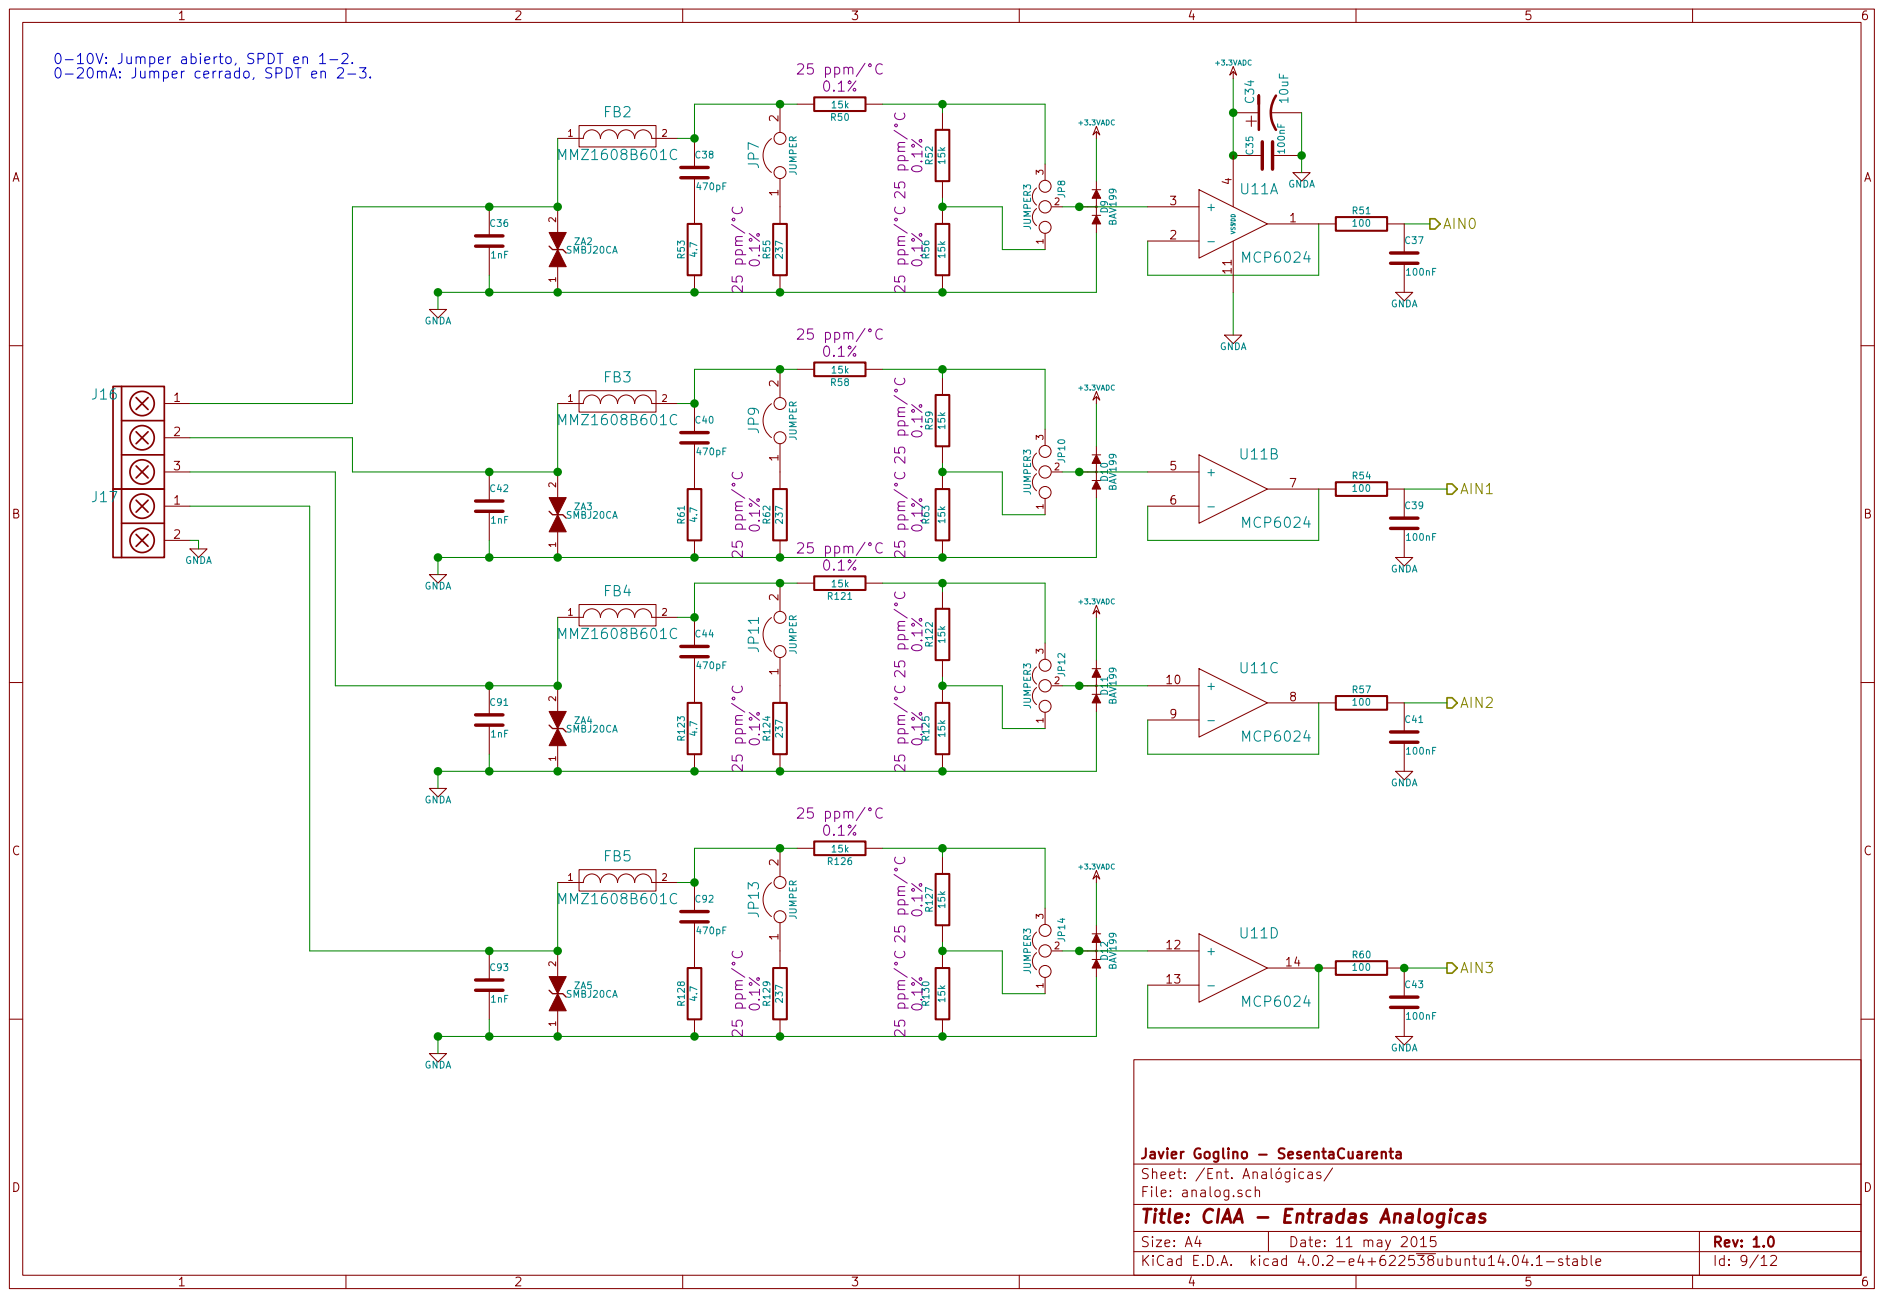
[picture p190: page 9]

0-10V: Jumper abierto, SPDT en 1-2.

Javier Goglino - SesentaCuarenta
Sheet: /Ent. Analógicas/
File: analog.sch
Id: 9/12 Title: CIAA - Entradas Analogicas

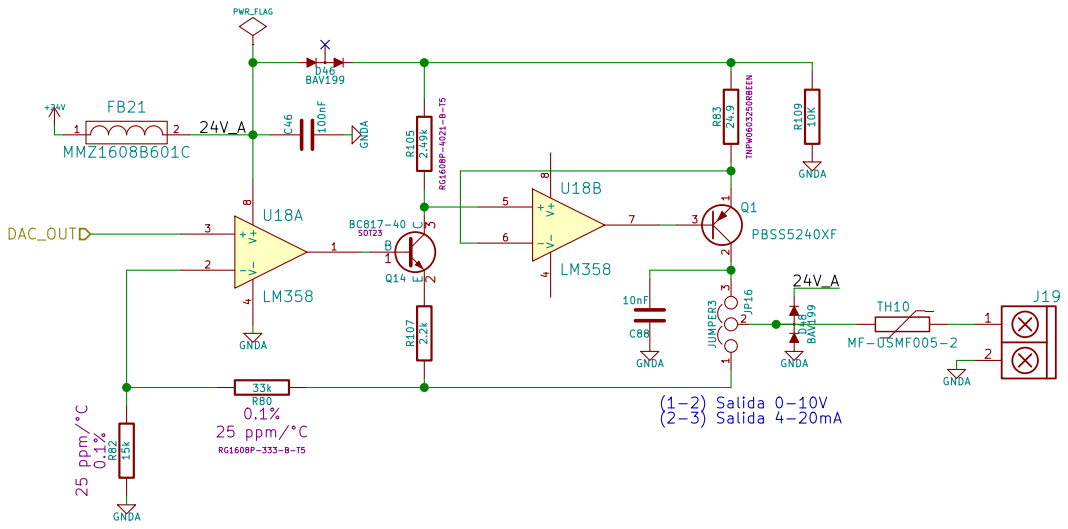
[picture p191: page 10]

Sheet: /Salida Analógica/
File: analog_out.sch
Id: 10/12 Title: CIAA - Salida Analógica

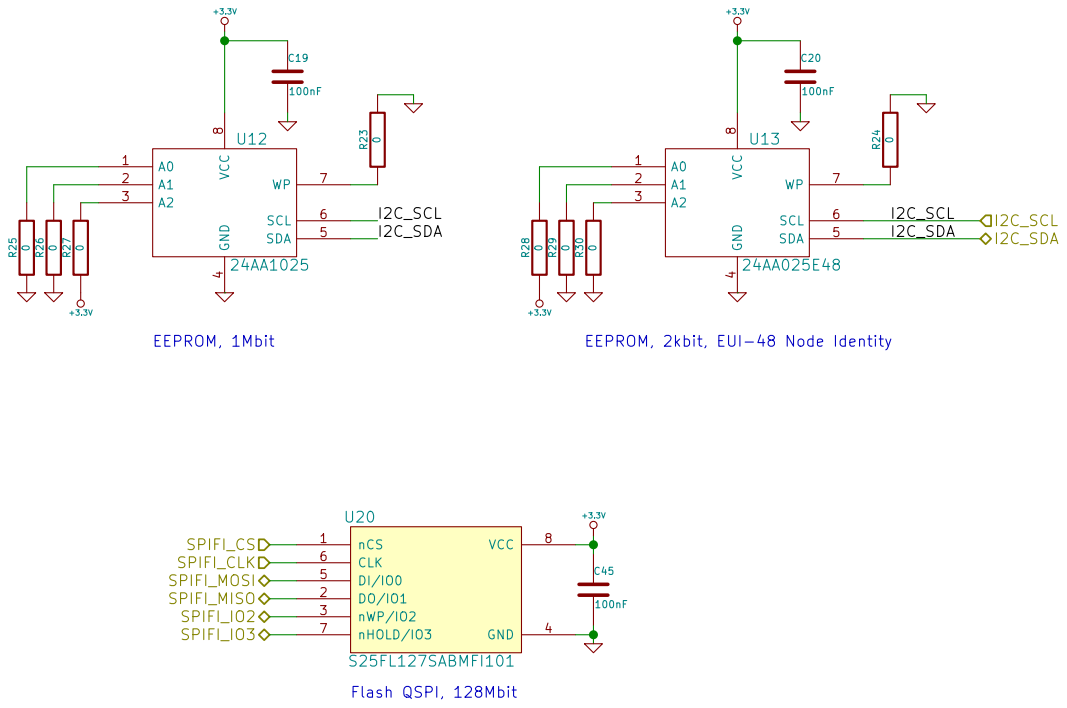
[picture p192: page 11]

File: mem.sch Sheet: /Memorias NV/ GND

Id: 11/12 Title: CIAA micro SD card

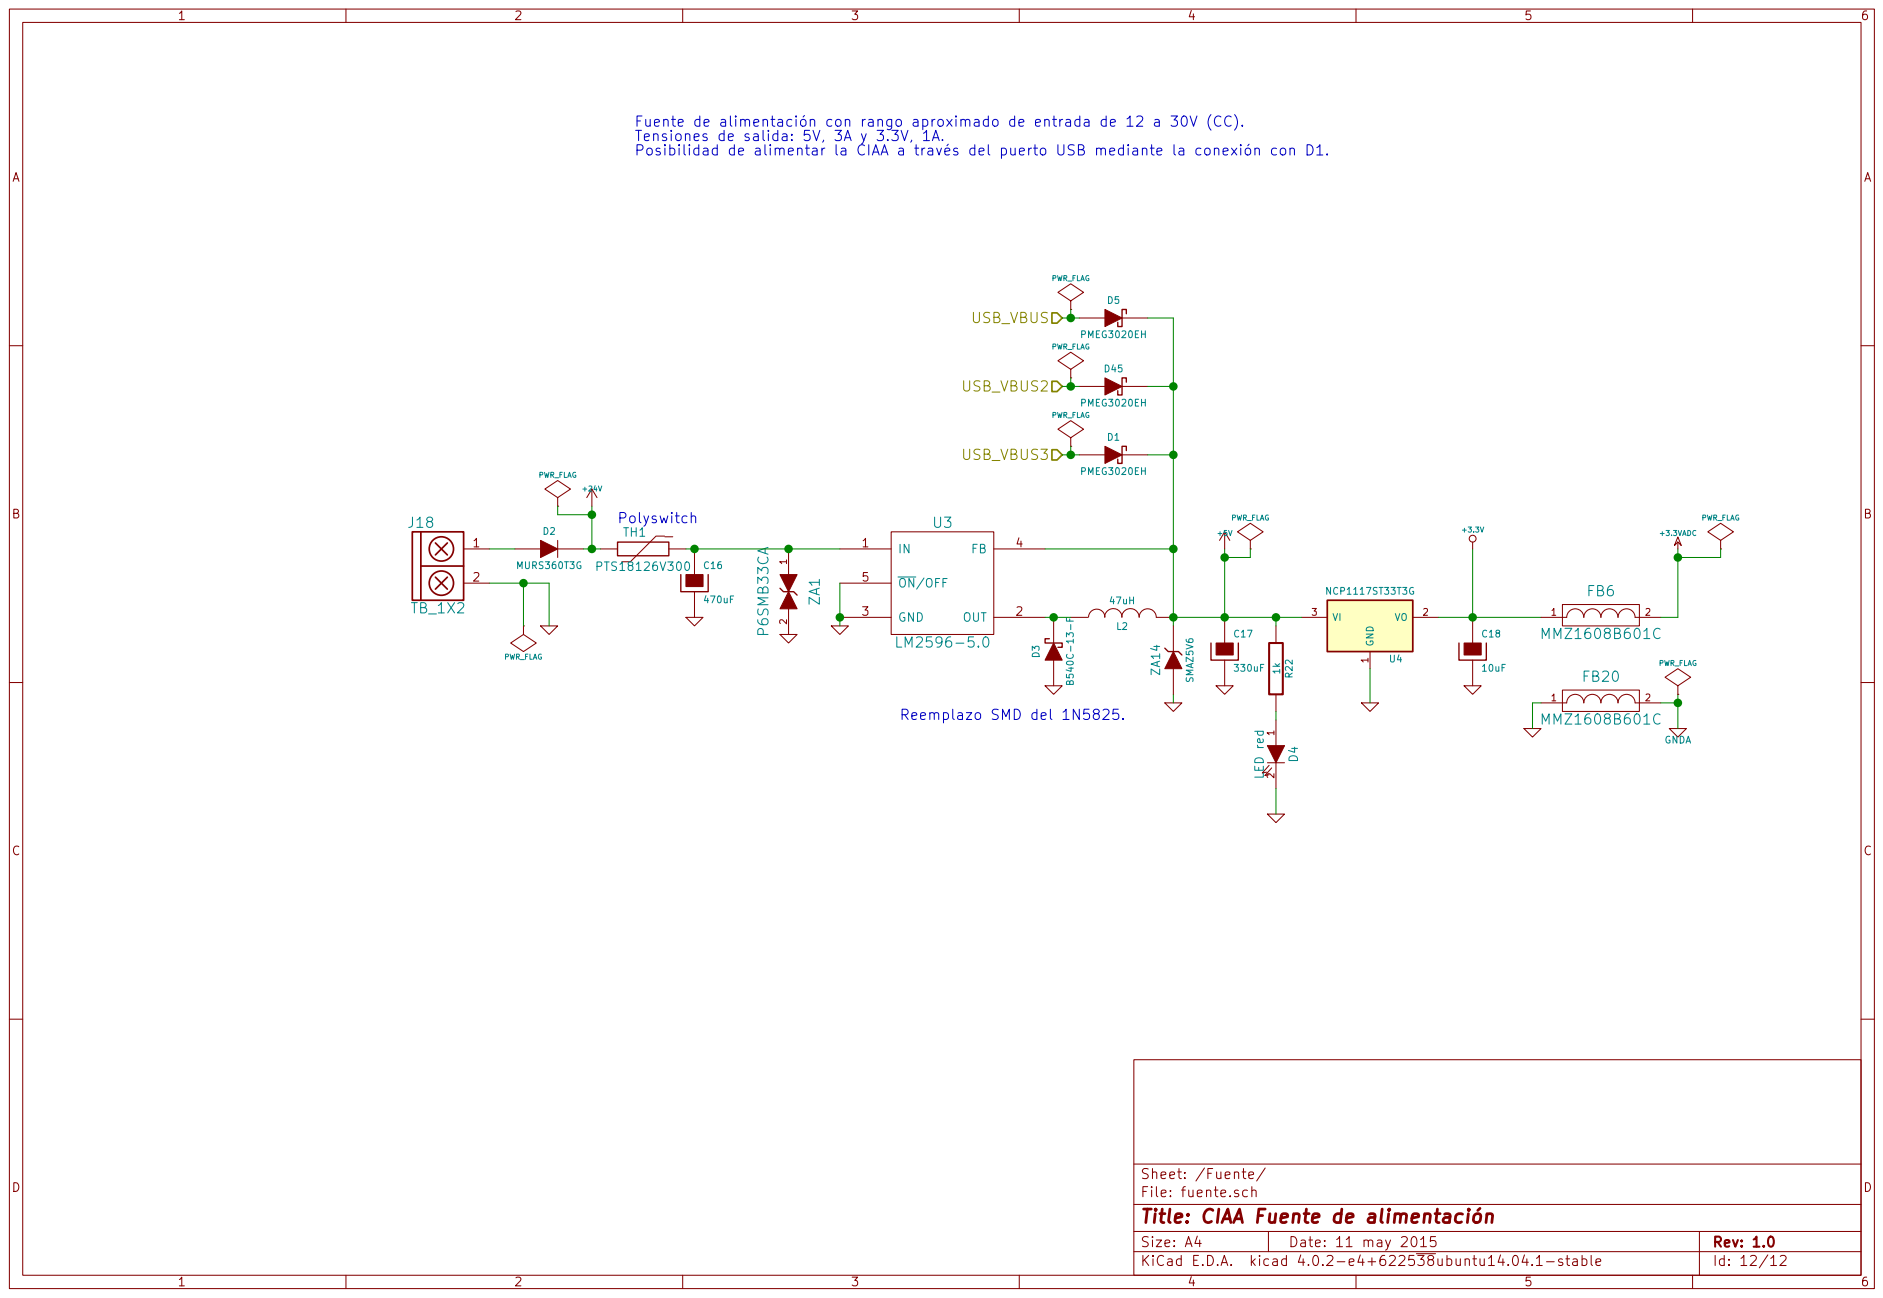
[picture p193: page 12]

Fuente de alimentación con rango aproximado de entrada de 12 a 30V (CC).
Tensiones de salida: 5V, 3A y 3.3V, 1A.
Posibilidad de alimentar la CIAA a través del puerto USB mediante la conexión con D1.

Id: 12/12 Title: CIAA Fuente de alimentación
