agumurray/G8-TP1/firmware_v3/documentation/CIAA_Boards/NXP_LPC4337/CIAA-NXP/CIAA-NXP v1.0 Board - 2019-01-04 v3r0.pdf

100M | LINK

# Especificaciones CIAA-NXP v1.0 - Frente

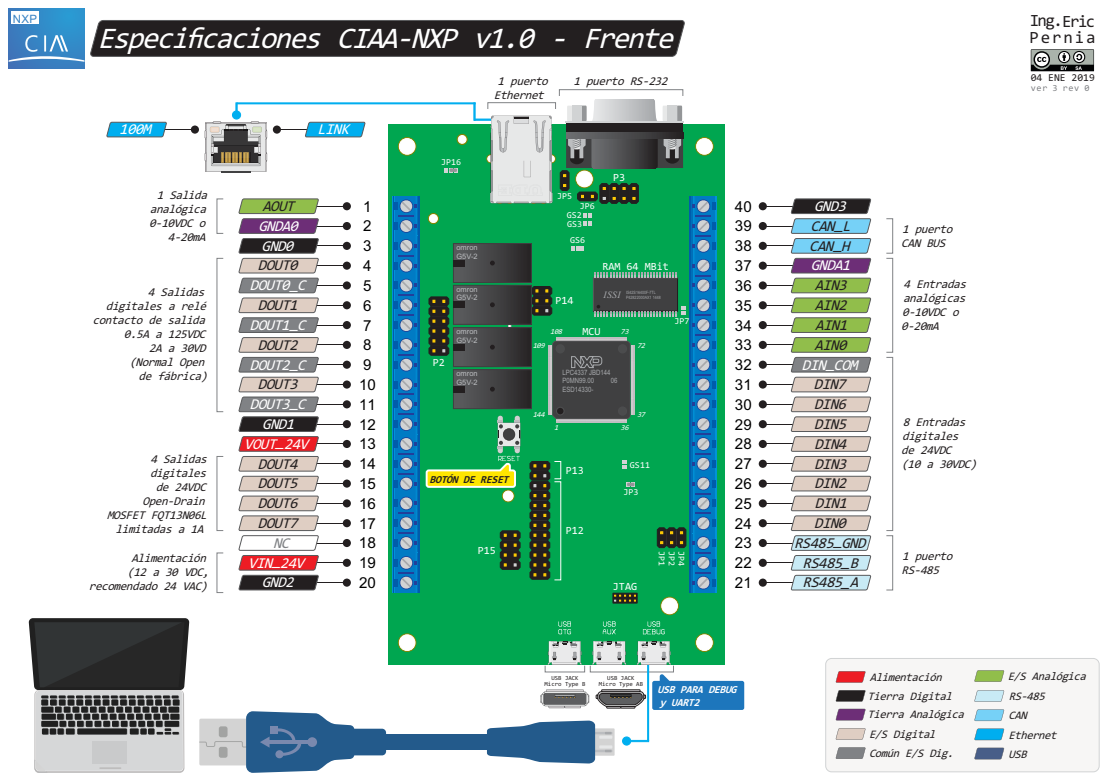
[picture p194: page 1]

JP16
GS2

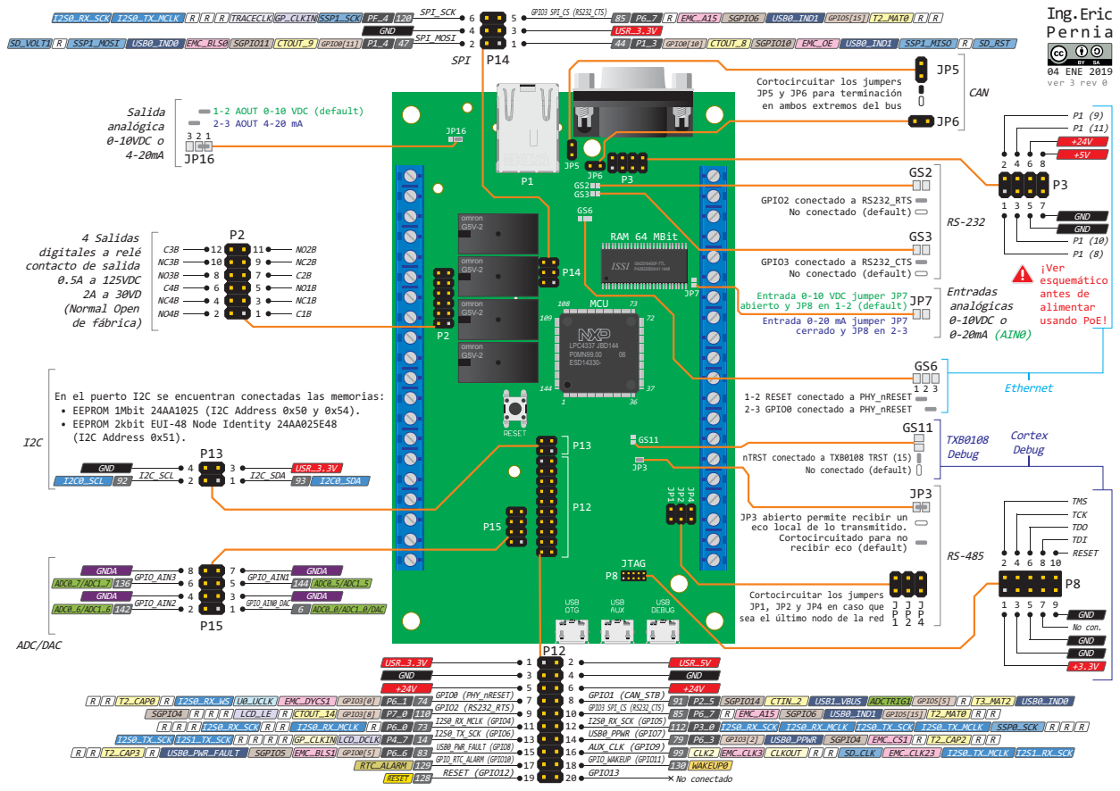
[picture p195: page 2]

SD VOLT1 R SSP1 MOSI USB0 IND0 EMC BLS0 SGPIO11 CTOUT 9 GPIO0[11] P1 4 47

44 P1 3 GPIO0[10] CTOUT 8 SGPIO10 EMC OE USB0 IND1 SSP1 MISO R SD RST

Cortocircuitar los jumpers
JP5 y JP6 para terminación
en ambos extremos del bus

En el puerto I2C se encuentran conectadas las memorias:
• EEPROM 1Mbit 24AA1025 (I2C Address 0x50 y 0x54).
• EEPROM 2kbit EUI-48 Node Identity 24AA025E48
(I2C Address 0x51).

JP3 abierto permite recibir un
eco local de lo transmitido.
Cortocircuitado para no
recibir eco (default)

JP1, JP2 y JP4 en caso que
sea el último nodo de la red

I2S0 RX MCLK I2S0 TX SCK I2S0 TX MCLK SSP0 SCK R R R

# Especificaciones CIAA-NXP v1.0 - Dorso

JP14

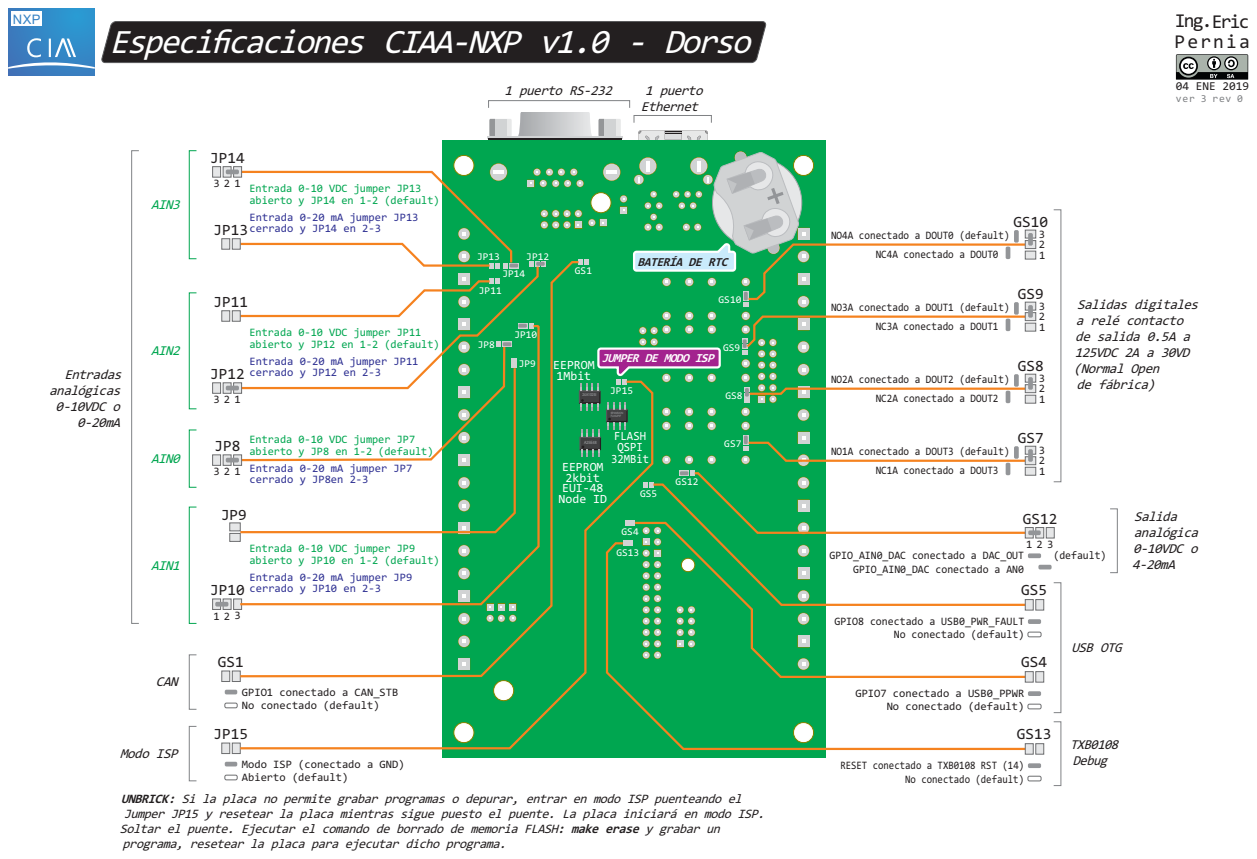
[picture p196: page 3]

JUMPER DE MODO ISP

Modo ISP (conectado a GND)
Abierto (default)

UNBRICK: Si la placa no permite grabar programas o depurar, entrar en modo ISP puenteando el
Jumper JP15 y resetear la placa mientras sigue puesto el puente. La placa iniciará en modo ISP.
Soltar el puente. Ejecutar el comando de borrado de memoria FLASH: make erase y grabar un
programa, resetear la placa para ejecutar dicho programa.

# Especificaciones CIAA-NXP v1.0 - Características

- Proyecto CIAA
http://proyecto-ciaa.com.ar
- Especificaciones CIAA-NXP http://proyecto-ciaa.com.ar/devwiki/doku.php?id=desarrollo:hardware:ciaa_nxp:ciaa_nxp_inicio
- Esquemático de la CIAA-NXP https://github.com/ciaa/Hardware/raw/master/PCB/NXP/docs/
ciaa-nxp.pdf
- Información del microcontrolador http://www.nxp.com/products/microcontrollers-and-processors/arm-processors/lpc-cortex-m-mcus/lpc-low-power-cortex-m4-mcus/lpc4300-cortex-m4-m0-mcus/32-bit-arm-cortex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
- Instalación de CIAA Firmware http://proyecto-ciaa.com.ar/devwiki/doku.php?id=docu:fw:bm:ide:install
- Software PLC IDE4PLC
https://ide4plc.wordpress.com/

CPU

Microcontrolador NXP LPC 4337 JDB 144 (Dual-core Cortex-M4 + Cortex-M0 @ 204MHz). Memoria SDRAM IS42S16400F. 64Mbit @ 143MHz.

DEBUGGER

USB-to-JTAG FT2232H. Soportado por OpenOCD.
Memoria EEPROM (utilizada por el FT2232H) AT93C46DN.
Conector Cortex-Debug para conectarle un Debugger externo.
Buffer TXB0108 para desconectar el FT2232H del bus JTAG en caso que se use Debugger externo.

MEMORIAS

- Memorias internas del LPC4337.
- SDRAM 128 Mbit (IS42S16800F-7TL o compatible).
- Flash SPI, 32 Mbit, Quad I/O FAST_READ: 80 MHz clock rate or 40 MB/s effective data rate. S25FL032P0XMFI011.
- EEPROM I2C 1 Mbit, 400 kHz. Almacenamiento de propósito general, datos de calibración del usuario, etc. 24AA1025.
- EEPROM I2C 2 kbit, 400 kHz. Unique Node Address EUI-48 para implementación de MAC-Address. Almacenamiento de propósito general. 24AA025E48

ENTRADAS DIGITALES

8 entradas digitales optoaisladas.
Rango de tensión de entrada asegurado 5VDC a 30VDC.
LED testigo en cada entrada.
Corriente de entrada máxima asegurada de 10mA, por regulador de corriente constante. Protección contra polaridad invertida o tensiones negativas.
Protección contra transitorios.

ENTRADAS ANALOGICAS

4 entradas analógicas configurables por Corriente/Tensión.
Lazo de corriente 4-20mA (con rango extendido 0-22mA), impedancia de carga 237 Ohm. Control por tensión 0-10V, impedancia de entrada 45 KOhm.
Protección contra transitorios.
Protección por filtrado de alta frecuencia.
Protección por diodos de enclavamiento. Amplificador-Buffer, estable y Rail-to-Rail.
Optimizado para aprovechar el rango del ADC (10 Bits).

04 ENE 2019
ver 3 rev 0

# CIAA-NXP v1.0 Pines utilizados del NXP LPC4337 JBD144 (1 a 72)

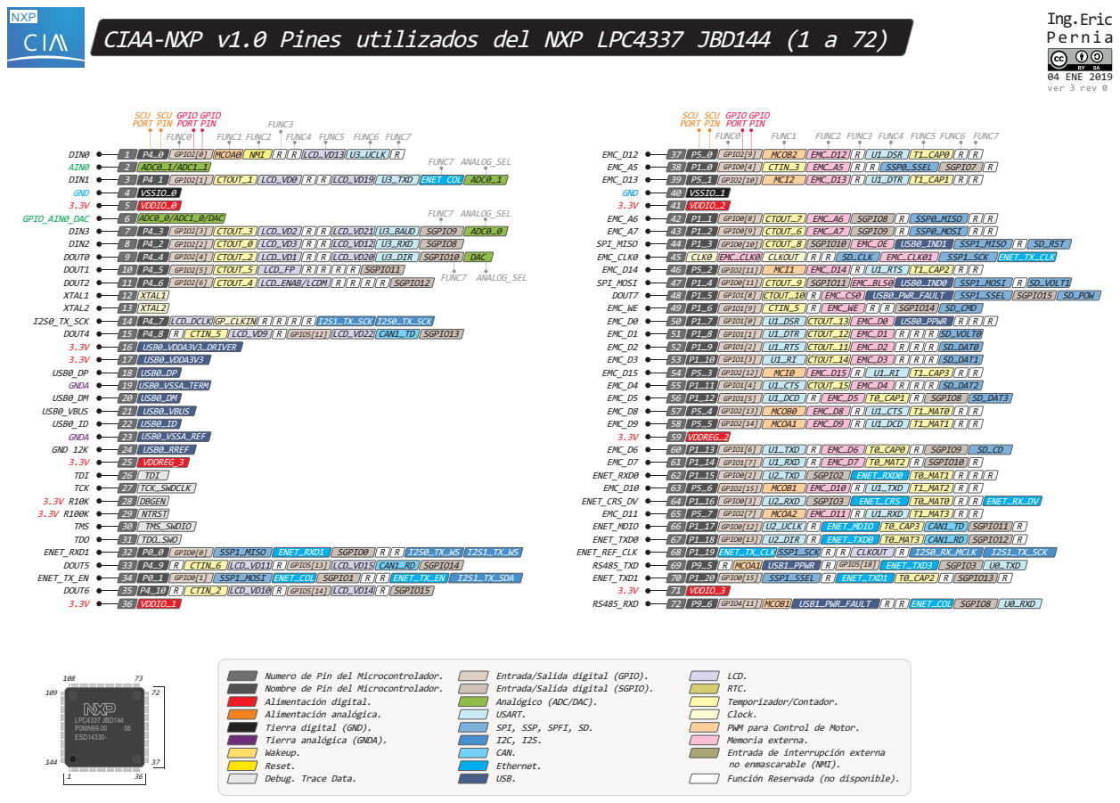
[picture p197: page 5]

LCD DCLK GP CLKIN R R R R

I2S1 TX SCK I2S0 TX SCK

Numero de Pin del Microcontrolador.
Nombre de Pin del Microcontrolador.
Alimentación digital.
Alimentación analógica.
Tierra digital (GND).
Tierra analógica (GNDA).
Wakeup.
Debug. Trace Data.

Entrada/Salida digital (GPIO).
Entrada/Salida digital (SGPIO).
USART.
SPI, SSP, SPFI, SD.
CAN.
Ethernet.
USB.

Clock.
PWM para Control de Motor.
Memoria externa.
Entrada de interrupción externa

Función Reservada (no disponible).

# CIAA-NXP v1.0 Pines utilizados del NXP LPC4337 JBD144 (73 a 144)

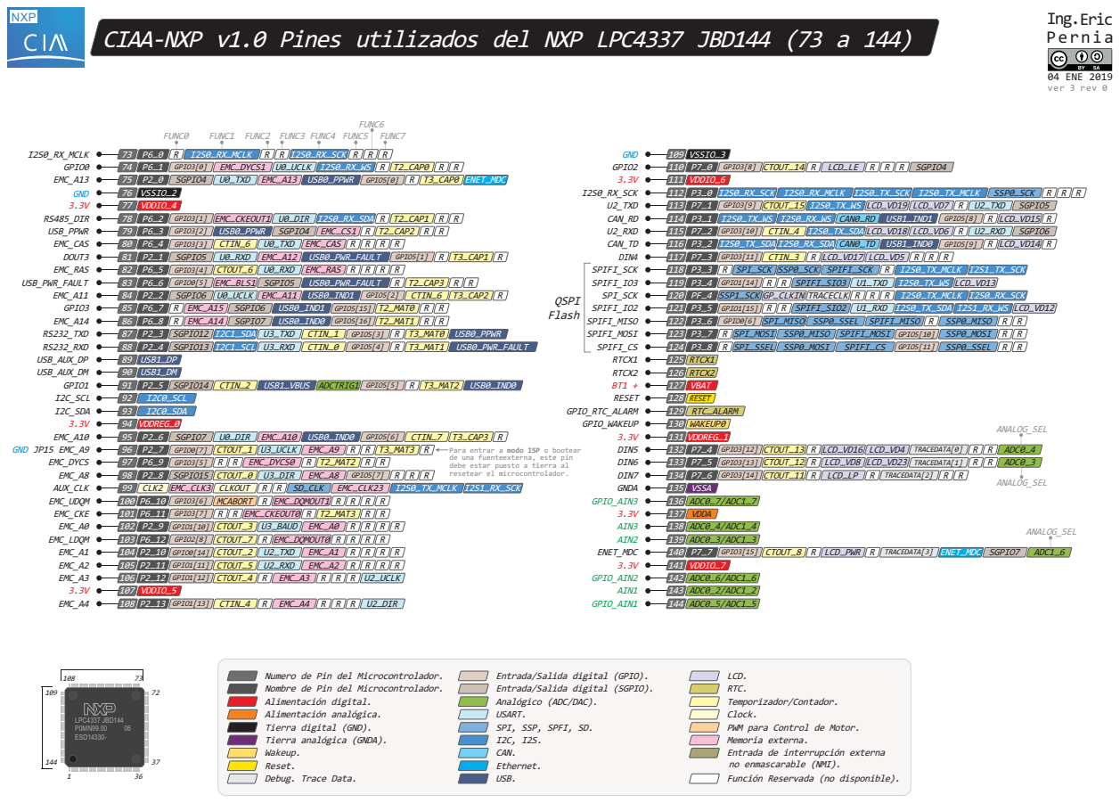
[picture p198: page 6]

82 P6 5 GPIO3[4] CTOUT 6 U0 RXD EMC RAS R R R R

de una fuenteexterna, este pin
debe estar puesto a tierra al
resetear el microcontrolador.

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

Entrada/Salida digital (GPIO).
Entrada/Salida digital (SGPIO).
USART.
SPI, SSP, SPFI, SD.
CAN.
Ethernet.
USB.

Clock.
PWM para Control de Motor.
Memoria externa.
Entrada de interrupción externa

Función Reservada (no disponible).
