agumurray/G8-TP1/firmware_v3/documentation/CIAA_Boards/NXP_LPC4337/EDU-CIAA-NXP/EDU-CIAA-NXP Mapeo de pines Firmata4CIAA v2.pdf

## Pernia

## Ing.Eric

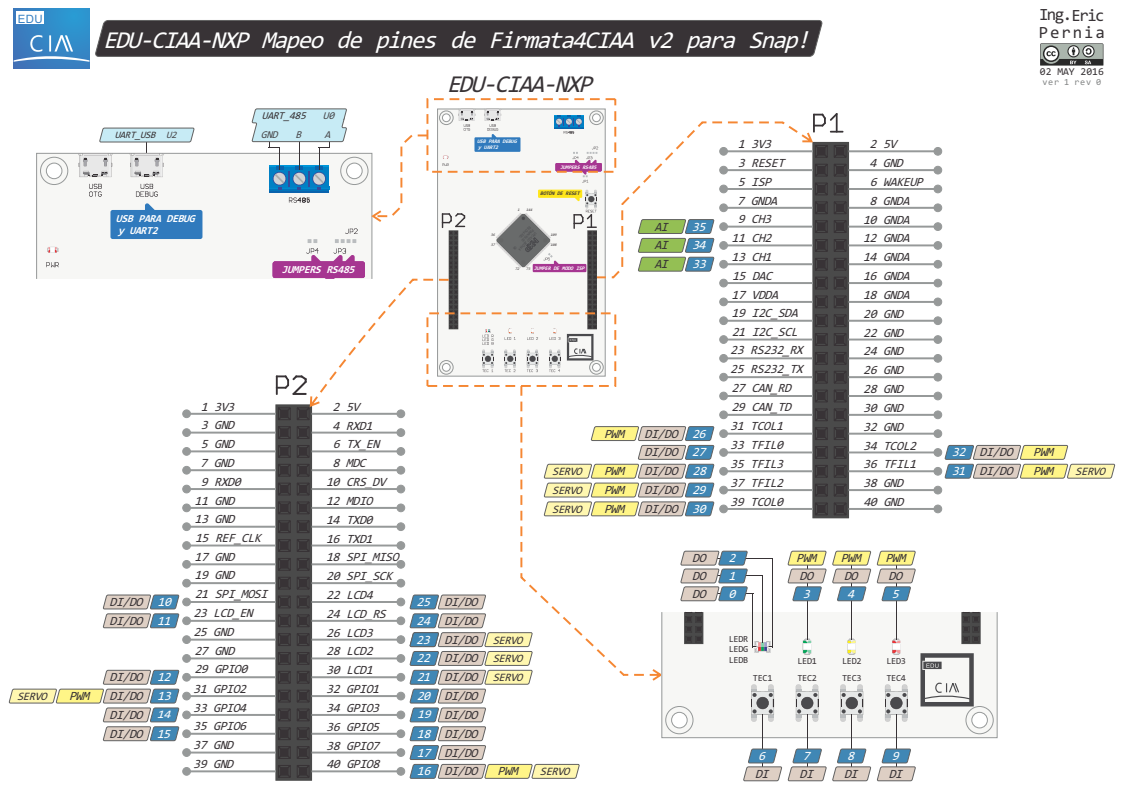
[picture p199: page 1]
EDU; 02 MAY 2016 ver 1 rev 0; PWM; SERVO; 18 SPI_MISO; 8 MDC; 10 CRS_DV; 12 MDIO; 14 TXD0; 16 TXD1; 34 GPIO3; 36 GPIO5; 32 GPIO1; 20 SPI_SCK; 22 LCD4; 24 LCD_RS; 4 RXD1; 26 LCD3; 28 LCD2; 30 LCD1; 40 GPIO8; 38 GPIO7; 23 LCD_EN; 25 GND; 31 GPIO2; 33 GPIO4; 35 GPIO6; 37 GND; 39 GND; 7 GND; 5 GND; 3 GND; 9 RXD0; 11 GND; 13 GND; 15 REF_CLK; 17 GND; 19 GND; 21 SPI_MOSI; 27 GND; 29 GPIO0; 18 GNDA; 8 GNDA; 10 GNDA; 12 GNDA; 14 GNDA; 16 GNDA; 6 WAKEUP; 34 TCOL2; 36 TFIL1; 32 GND; 20 GND; 22 GND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

EDU-CIAA-NXP Mapeo de pines de Firmata4CIAA v2 para Snap!

EDU-CIAA-NXP

USB PARA DEBUG
y UART2

BOTÓN DE RESET

JUMPER DE MODO ISP
