agumurray/G8-TP1/firmware_v3/maze-solver-robot/app/inc/wall_follower.h

#ifndef WALL_FOLLOWER_H_
#define WALL_FOLLOWER_H_

#include "sapi.h"

// Inicialización general del algoritmo
void wall_follower_init(void);

// Lógica principal a ejecutar periódicamente
void wall_follower_step(void);

void wall_follower_try(void);

#endif
